prudhvibelide/BLE-Fitness-Tracker/Firmware/config/pin_config.h

#ifndef PIN_CONFIG_H
#define PIN_CONFIG_H

// $[CMU]
// [CMU]$

// $[LFXO]
// LFXO LFXTAL_I on PD01
#ifndef LFXO_LFXTAL_I_PORT                      
#define LFXO_LFXTAL_I_PORT                       gpioPortD
#endif
#ifndef LFXO_LFXTAL_I_PIN                       
#define LFXO_LFXTAL_I_PIN                        1
#endif

// LFXO LFXTAL_O on PD00
#ifndef LFXO_LFXTAL_O_PORT                      
#define LFXO_LFXTAL_O_PORT                       gpioPortD
#endif
#ifndef LFXO_LFXTAL_O_PIN                       
#define LFXO_LFXTAL_O_PIN                        0
#endif

// [LFXO]$

// $[PRS.ASYNCH0]
// [PRS.ASYNCH0]$

// $[PRS.ASYNCH1]
// [PRS.ASYNCH1]$

// $[PRS.ASYNCH2]
// [PRS.ASYNCH2]$

// $[PRS.ASYNCH3]
// [PRS.ASYNCH3]$

// $[PRS.ASYNCH4]
// [PRS.ASYNCH4]$

// $[PRS.ASYNCH5]
// [PRS.ASYNCH5]$

// $[PRS.ASYNCH6]
// [PRS.ASYNCH6]$

// $[PRS.ASYNCH7]
// [PRS.ASYNCH7]$

// $[PRS.ASYNCH8]
// [PRS.ASYNCH8]$

// $[PRS.ASYNCH9]
// [PRS.ASYNCH9]$

// $[PRS.ASYNCH10]
// [PRS.ASYNCH10]$

// $[PRS.ASYNCH11]
// [PRS.ASYNCH11]$

// $[PRS.ASYNCH12]
// [PRS.ASYNCH12]$

// $[PRS.ASYNCH13]
// [PRS.ASYNCH13]$

// $[PRS.ASYNCH14]
// [PRS.ASYNCH14]$

// $[PRS.ASYNCH15]
// [PRS.ASYNCH15]$

// $[PRS.SYNCH0]
// [PRS.SYNCH0]$

// $[PRS.SYNCH1]
// [PRS.SYNCH1]$

// $[PRS.SYNCH2]
// [PRS.SYNCH2]$

// $[PRS.SYNCH3]
// [PRS.SYNCH3]$

// $[GPIO]
// [GPIO]$

// $[TIMER0]
// [TIMER0]$

// $[TIMER1]
// [TIMER1]$

// $[TIMER2]
// [TIMER2]$

// $[TIMER3]
// [TIMER3]$

// $[TIMER4]
// [TIMER4]$

// $[USART0]
// [USART0]$

// $[I2C1]
// [I2C1]$

// $[EUSART1]
// [EUSART1]$

// $[KEYSCAN]
// [KEYSCAN]$

// $[LETIMER0]
// [LETIMER0]$

// $[IADC0]
// [IADC0]$

// $[ACMP0]
// [ACMP0]$

// $[ACMP1]
// [ACMP1]$

// $[VDAC0]
// [VDAC0]$

// $[VDAC1]
// [VDAC1]$

// $[PCNT0]
// [PCNT0]$

// $[HFXO0]
// [HFXO0]$

// $[I2C0]
// [I2C0]$

// $[EUSART0]
// [EUSART0]$

// $[PTI]
// [PTI]$

// $[MODEM]
// [MODEM]$

// $[CUSTOM_PIN_NAME]
#ifndef _PORT                                   
#define _PORT                                    gpioPortA
#endif
#ifndef _PIN                                    
#define _PIN                                     0
#endif

// [CUSTOM_PIN_NAME]$

#endif // PIN_CONFIG_H
