prudhvibelide/BLE-Fitness-Tracker/Firmware/gecko_sdk_4.4.4/platform/emlib/inc/em_adc.h

/***************************************************************************//**
 * @file
 * @brief Analog to Digital Converter (ADC) peripheral API
 *******************************************************************************
 * # License
 * <b>Copyright 2018 Silicon Laboratories Inc. www.silabs.com</b>
 *******************************************************************************
 *
 * SPDX-License-Identifier: Zlib
 *
 * The licensor of this software is Silicon Laboratories Inc.
 *
 * This software is provided 'as-is', without any express or implied
 * warranty. In no event will the authors be held liable for any damages
 * arising from the use of this software.
 *
 * Permission is granted to anyone to use this software for any purpose,
 * including commercial applications, and to alter it and redistribute it
 * freely, subject to the following restrictions:
 *
 * 1. The origin of this software must not be misrepresented; you must not
 *    claim that you wrote the original software. If you use this software
 *    in a product, an acknowledgment in the product documentation would be
 *    appreciated but is not required.
 * 2. Altered source versions must be plainly marked as such, and must not be
 *    misrepresented as being the original software.
 * 3. This notice may not be removed or altered from any source distribution.
 *
 ******************************************************************************/

#ifndef EM_ADC_H
#define EM_ADC_H

#include "em_device.h"
#if defined(ADC_COUNT) && (ADC_COUNT > 0)

#include <stdbool.h>

#ifdef __cplusplus
extern "C" {
#endif

/***************************************************************************//**
 * @addtogroup adc
 * @{
 ******************************************************************************/

/*******************************************************************************
 ********************************   ENUMS   ************************************
 ******************************************************************************/

/** Acquisition time (in ADC clock cycles). */
typedef enum {
  adcAcqTime1   = _ADC_SINGLECTRL_AT_1CYCLE,    /**< 1 clock cycle. */
  adcAcqTime2   = _ADC_SINGLECTRL_AT_2CYCLES,   /**< 2 clock cycles. */
  adcAcqTime4   = _ADC_SINGLECTRL_AT_4CYCLES,   /**< 4 clock cycles. */
  adcAcqTime8   = _ADC_SINGLECTRL_AT_8CYCLES,   /**< 8 clock cycles. */
  adcAcqTime16  = _ADC_SINGLECTRL_AT_16CYCLES,  /**< 16 clock cycles. */
  adcAcqTime32  = _ADC_SINGLECTRL_AT_32CYCLES,  /**< 32 clock cycles. */
  adcAcqTime64  = _ADC_SINGLECTRL_AT_64CYCLES,  /**< 64 clock cycles. */
  adcAcqTime128 = _ADC_SINGLECTRL_AT_128CYCLES, /**< 128 clock cycles. */
  adcAcqTime256 = _ADC_SINGLECTRL_AT_256CYCLES  /**< 256 clock cycles. */
} ADC_AcqTime_TypeDef;

#if defined(_ADC_CTRL_LPFMODE_MASK)
/** Lowpass filter mode. */
typedef enum {
  /** No filter or decoupling capacitor. */
  adcLPFilterBypass = _ADC_CTRL_LPFMODE_BYPASS,

  /** On-chip RC filter. */
  adcLPFilterRC     = _ADC_CTRL_LPFMODE_RCFILT,

  /** On-chip decoupling capacitor. */
  adcLPFilterDeCap  = _ADC_CTRL_LPFMODE_DECAP
} ADC_LPFilter_TypeDef;
#endif

/** Oversample rate select. */
typedef enum {
  /** 2 samples per conversion result. */
  adcOvsRateSel2    = _ADC_CTRL_OVSRSEL_X2,

  /** 4 samples per conversion result. */
  adcOvsRateSel4    = _ADC_CTRL_OVSRSEL_X4,

  /** 8 samples per conversion result. */
  adcOvsRateSel8    = _ADC_CTRL_OVSRSEL_X8,

  /** 16 samples per conversion result. */
  adcOvsRateSel16   = _ADC_CTRL_OVSRSEL_X16,

  /** 32 samples per conversion result. */
  adcOvsRateSel32   = _ADC_CTRL_OVSRSEL_X32,

  /** 64 samples per conversion result. */
  adcOvsRateSel64   = _ADC_CTRL_OVSRSEL_X64,

  /** 128 samples per conversion result. */
  adcOvsRateSel128  = _ADC_CTRL_OVSRSEL_X128,

  /** 256 samples per conversion result. */
  adcOvsRateSel256  = _ADC_CTRL_OVSRSEL_X256,

  /** 512 samples per conversion result. */
  adcOvsRateSel512  = _ADC_CTRL_OVSRSEL_X512,

  /** 1024 samples per conversion result. */
  adcOvsRateSel1024 = _ADC_CTRL_OVSRSEL_X1024,

  /** 2048 samples per conversion result. */
  adcOvsRateSel2048 = _ADC_CTRL_OVSRSEL_X2048,

  /** 4096 samples per conversion result. */
  adcOvsRateSel4096 = _ADC_CTRL_OVSRSEL_X4096
} ADC_OvsRateSel_TypeDef;

/** Peripheral Reflex System signal used to trigger a single sample. */
typedef enum {
#if defined(_ADC_SINGLECTRL_PRSSEL_MASK)
  adcPRSSELCh0 = _ADC_SINGLECTRL_PRSSEL_PRSCH0, /**< PRS channel 0. */
  adcPRSSELCh1 = _ADC_SINGLECTRL_PRSSEL_PRSCH1, /**< PRS channel 1. */
  adcPRSSELCh2 = _ADC_SINGLECTRL_PRSSEL_PRSCH2, /**< PRS channel 2. */
  adcPRSSELCh3 = _ADC_SINGLECTRL_PRSSEL_PRSCH3, /**< PRS channel 3. */
#if defined(_ADC_SINGLECTRL_PRSSEL_PRSCH4)
  adcPRSSELCh4 = _ADC_SINGLECTRL_PRSSEL_PRSCH4, /**< PRS channel 4. */
#endif
#if defined(_ADC_SINGLECTRL_PRSSEL_PRSCH5)
  adcPRSSELCh5 = _ADC_SINGLECTRL_PRSSEL_PRSCH5, /**< PRS channel 5. */
#endif
#if defined(_ADC_SINGLECTRL_PRSSEL_PRSCH6)
  adcPRSSELCh6 = _ADC_SINGLECTRL_PRSSEL_PRSCH6, /**< PRS channel 6. */
#endif
#if defined(_ADC_SINGLECTRL_PRSSEL_PRSCH7)
  adcPRSSELCh7 = _ADC_SINGLECTRL_PRSSEL_PRSCH7, /**< PRS channel 7. */
#endif
#if defined(_ADC_SINGLECTRL_PRSSEL_PRSCH8)
  adcPRSSELCh8 = _ADC_SINGLECTRL_PRSSEL_PRSCH8, /**< PRS channel 8. */
#endif
#if defined(_ADC_SINGLECTRL_PRSSEL_PRSCH9)
  adcPRSSELCh9 = _ADC_SINGLECTRL_PRSSEL_PRSCH9, /**< PRS channel 9. */
#endif
#if defined(_ADC_SINGLECTRL_PRSSEL_PRSCH10)
  adcPRSSELCh10 = _ADC_SINGLECTRL_PRSSEL_PRSCH10, /**< PRS channel 10. */
#endif
#if defined(_ADC_SINGLECTRL_PRSSEL_PRSCH11)
  adcPRSSELCh11 = _ADC_SINGLECTRL_PRSSEL_PRSCH11, /**< PRS channel 11. */
#endif
#elif defined(_ADC_SINGLECTRLX_PRSSEL_MASK)
  adcPRSSELCh0 = _ADC_SINGLECTRLX_PRSSEL_PRSCH0, /**< PRS channel 0. */
  adcPRSSELCh1 = _ADC_SINGLECTRLX_PRSSEL_PRSCH1, /**< PRS channel 1. */
  adcPRSSELCh2 = _ADC_SINGLECTRLX_PRSSEL_PRSCH2, /**< PRS channel 2. */
  adcPRSSELCh3 = _ADC_SINGLECTRLX_PRSSEL_PRSCH3, /**< PRS channel 3. */
  adcPRSSELCh4 = _ADC_SINGLECTRLX_PRSSEL_PRSCH4, /**< PRS channel 4. */
  adcPRSSELCh5 = _ADC_SINGLECTRLX_PRSSEL_PRSCH5, /**< PRS channel 5. */
  adcPRSSELCh6 = _ADC_SINGLECTRLX_PRSSEL_PRSCH6, /**< PRS channel 6. */
  adcPRSSELCh7 = _ADC_SINGLECTRLX_PRSSEL_PRSCH7,  /**< PRS channel 7. */
#if defined(_ADC_SINGLECTRLX_PRSSEL_PRSCH8)
  adcPRSSELCh8 = _ADC_SINGLECTRLX_PRSSEL_PRSCH8,  /**< PRS channel 8. */
#endif
#if defined(_ADC_SINGLECTRLX_PRSSEL_PRSCH9)
  adcPRSSELCh9 = _ADC_SINGLECTRLX_PRSSEL_PRSCH9,  /**< PRS channel 9. */
#endif
#if defined(_ADC_SINGLECTRLX_PRSSEL_PRSCH10)
  adcPRSSELCh10 = _ADC_SINGLECTRLX_PRSSEL_PRSCH10,  /**< PRS channel 10. */
#endif
#if defined(_ADC_SINGLECTRLX_PRSSEL_PRSCH11)
  adcPRSSELCh11 = _ADC_SINGLECTRLX_PRSSEL_PRSCH11,  /**< PRS channel 11. */
#endif
#if defined(_ADC_SINGLECTRLX_PRSSEL_PRSCH12)
  adcPRSSELCh12 = _ADC_SINGLECTRLX_PRSSEL_PRSCH12,  /**< PRS channel 12. */
  adcPRSSELCh13 = _ADC_SINGLECTRLX_PRSSEL_PRSCH13,  /**< PRS channel 13. */
  adcPRSSELCh14 = _ADC_SINGLECTRLX_PRSSEL_PRSCH14,  /**< PRS channel 14. */
  adcPRSSELCh15 = _ADC_SINGLECTRLX_PRSSEL_PRSCH15,  /**< PRS channel 15. */
#endif
#endif
} ADC_PRSSEL_TypeDef;

/** Single and scan mode voltage references. Using unshifted enumerations and or
    in ADC_CTRLX_VREFSEL_REG to select the extension register CTRLX_VREFSEL. */
#if defined(_ADC_SCANCTRLX_VREFSEL_MASK)
#define ADC_CTRLX_VREFSEL_REG     0x80UL
#endif
/** ADC Reference */
typedef enum {
  /** Internal 1.25 V reference. */
  adcRef1V25      = _ADC_SINGLECTRL_REF_1V25,

  /** Internal 2.5 V reference. */
  adcRef2V5       = _ADC_SINGLECTRL_REF_2V5,

  /** Buffered VDD. */
  adcRefVDD       = _ADC_SINGLECTRL_REF_VDD,

#if defined(_ADC_SINGLECTRL_REF_5VDIFF)
  /** Internal differential 5 V reference. */
  adcRef5VDIFF    = _ADC_SINGLECTRL_REF_5VDIFF,
#endif

#if defined(_ADC_SINGLECTRL_REF_5V)
  /** Internal 5 V reference. */
  adcRef5V        = _ADC_SINGLECTRL_REF_5V,
#endif

  /** Single-ended external reference from pin 6. */
  adcRefExtSingle = _ADC_SINGLECTRL_REF_EXTSINGLE,

  /** Differential external reference from pin 6 and 7. */
  adcRef2xExtDiff = _ADC_SINGLECTRL_REF_2XEXTDIFF,

  /** Unbuffered 2xVDD. */
  adcRef2xVDD     = _ADC_SINGLECTRL_REF_2XVDD,

#if defined(_ADC_SINGLECTRLX_VREFSEL_VBGR)
  /** Custom VFS: Internal Bandgap reference. */
  adcRefVBGR      = _ADC_SINGLECTRLX_VREFSEL_VBGR | ADC_CTRLX_VREFSEL_REG,
#endif

#if defined(_ADC_SINGLECTRLX_VREFSEL_VDDXWATT)
  /** Custom VFS: Scaled AVDD: AVDD * VREFATT. */
  adcRefVddxAtt   = _ADC_SINGLECTRLX_VREFSEL_VDDXWATT | ADC_CTRLX_VREFSEL_REG,
#endif

#if defined(_ADC_SINGLECTRLX_VREFSEL_VREFPWATT)
  /** Custom VFS: Scaled singled ended external reference from pin 6:
      VREFP * VREFATT. */
  adcRefVPxAtt    = _ADC_SINGLECTRLX_VREFSEL_VREFPWATT | ADC_CTRLX_VREFSEL_REG,
#endif

#if defined(_ADC_SINGLECTRLX_VREFSEL_VREFP)
  /** Custom VFS: Raw single-ended external reference from pin 6. */
  adcRefP         = _ADC_SINGLECTRLX_VREFSEL_VREFP | ADC_CTRLX_VREFSEL_REG,
#endif

#if defined(_ADC_SINGLECTRLX_VREFSEL_VENTROPY)
  /** Custom VFS: Special mode for entropy generation */
  adcRefVEntropy = _ADC_SINGLECTRLX_VREFSEL_VENTROPY | ADC_CTRLX_VREFSEL_REG,
#endif

#if defined(_ADC_SINGLECTRLX_VREFSEL_VREFPNWATT)
  /** Custom VFS: Scaled differential external Vref from pin 6 and 7:
      (VREFP - VREFN) * VREFATT. */
  adcRefVPNxAtt  = _ADC_SINGLECTRLX_VREFSEL_VREFPNWATT | ADC_CTRLX_VREFSEL_REG,
#endif

#if defined(_ADC_SINGLECTRLX_VREFSEL_VREFPN)
  /** Custom VFS: Raw differential external Vref from pin 6 and 7:
      VREFP - VREFN. */
  adcRefPN       = _ADC_SINGLECTRLX_VREFSEL_VREFPN | ADC_CTRLX_VREFSEL_REG,
#endif
} ADC_Ref_TypeDef;

/** @cond DO_NOT_INCLUDE_WITH_DOXYGEN */
/* Deprecated enum names */
#if !defined(_ADC_SINGLECTRL_REF_5VDIFF)
#define adcRef5VDIFF adcRef5V
#endif
/** @endcond */

/** Sample resolution. */
typedef enum {
  adcRes12Bit = _ADC_SINGLECTRL_RES_12BIT, /**< 12 bit sampling. */
  adcRes8Bit  = _ADC_SINGLECTRL_RES_8BIT,  /**< 8 bit sampling. */
  adcRes6Bit  = _ADC_SINGLECTRL_RES_6BIT,  /**< 6 bit sampling. */
  adcResOVS   = _ADC_SINGLECTRL_RES_OVS    /**< Oversampling. */
} ADC_Res_TypeDef;

#if defined(_ADC_SINGLECTRL_INPUTSEL_MASK)
/** Single sample input selection. */
typedef enum {
  /* Differential mode disabled */
  adcSingleInputCh0      = _ADC_SINGLECTRL_INPUTSEL_CH0,      /**< Channel 0. */
  adcSingleInputCh1      = _ADC_SINGLECTRL_INPUTSEL_CH1,      /**< Channel 1. */
  adcSingleInputCh2      = _ADC_SINGLECTRL_INPUTSEL_CH2,      /**< Channel 2. */
  adcSingleInputCh3      = _ADC_SINGLECTRL_INPUTSEL_CH3,      /**< Channel 3. */
  adcSingleInputCh4      = _ADC_SINGLECTRL_INPUTSEL_CH4,      /**< Channel 4. */
  adcSingleInputCh5      = _ADC_SINGLECTRL_INPUTSEL_CH5,      /**< Channel 5. */
  adcSingleInputCh6      = _ADC_SINGLECTRL_INPUTSEL_CH6,      /**< Channel 6. */
  adcSingleInputCh7      = _ADC_SINGLECTRL_INPUTSEL_CH7,      /**< Channel 7. */
  adcSingleInputTemp     = _ADC_SINGLECTRL_INPUTSEL_TEMP,     /**< Temperature reference. */
  adcSingleInputVDDDiv3  = _ADC_SINGLECTRL_INPUTSEL_VDDDIV3,  /**< VDD divided by 3. */
  adcSingleInputVDD      = _ADC_SINGLECTRL_INPUTSEL_VDD,      /**< VDD. */
  adcSingleInputVSS      = _ADC_SINGLECTRL_INPUTSEL_VSS,      /**< VSS. */
  adcSingleInputVrefDiv2 = _ADC_SINGLECTRL_INPUTSEL_VREFDIV2, /**< Vref divided by 2. */
  adcSingleInputDACOut0  = _ADC_SINGLECTRL_INPUTSEL_DAC0OUT0, /**< DAC output 0. */
  adcSingleInputDACOut1  = _ADC_SINGLECTRL_INPUTSEL_DAC0OUT1, /**< DAC output 1. */
  adcSingleInputATEST    = 15,                                /**< ATEST. */

  /* Differential mode enabled */
  adcSingleInputCh0Ch1   = _ADC_SINGLECTRL_INPUTSEL_CH0CH1,   /**< Positive Ch0, negative Ch1. */
  adcSingleInputCh2Ch3   = _ADC_SINGLECTRL_INPUTSEL_CH2CH3,   /**< Positive Ch2, negative Ch3. */
  adcSingleInputCh4Ch5   = _ADC_SINGLECTRL_INPUTSEL_CH4CH5,   /**< Positive Ch4, negative Ch5. */
  adcSingleInputCh6Ch7   = _ADC_SINGLECTRL_INPUTSEL_CH6CH7,   /**< Positive Ch6, negative Ch7. */
  adcSingleInputDiff0    = 4                                  /**< Differential 0. */
} ADC_SingleInput_TypeDef;

/** @cond DO_NOT_INCLUDE_WITH_DOXYGEN */
/* Deprecated enum names */
#define adcSingleInpCh0       adcSingleInputCh0
#define adcSingleInpCh1       adcSingleInputCh1
#define adcSingleInpCh2       adcSingleInputCh2
#define adcSingleInpCh3       adcSingleInputCh3
#define adcSingleInpCh4       adcSingleInputCh4
#define adcSingleInpCh5       adcSingleInputCh5
#define adcSingleInpCh6       adcSingleInputCh6
#define adcSingleInpCh7       adcSingleInputCh7
#define adcSingleInpTemp      adcSingleInputTemp
#define adcSingleInpVDDDiv3   adcSingleInputVDDDiv3
#define adcSingleInpVDD       adcSingleInputVDD
#define adcSingleInpVSS       adcSingleInputVSS
#define adcSingleInpVrefDiv2  adcSingleInputVrefDiv2
#define adcSingleInpDACOut0   adcSingleInputDACOut0
#define adcSingleInpDACOut1   adcSingleInputDACOut1
#define adcSingleInpATEST     adcSingleInputATEST
#define adcSingleInpCh0Ch1    adcSingleInputCh0Ch1
#define adcSingleInpCh2Ch3    adcSingleInputCh2Ch3
#define adcSingleInpCh4Ch5    adcSingleInputCh4Ch5
#define adcSingleInpCh6Ch7    adcSingleInputCh6Ch7
#define adcSingleInpDiff0     adcSingleInputDiff0
/** @endcond */
#endif

#if defined(_ADC_SINGLECTRL_POSSEL_MASK)
/** Positive input selection for single and scan conversion. */
typedef enum {
  adcPosSelAPORT0XCH0  = _ADC_SINGLECTRL_POSSEL_APORT0XCH0,
  adcPosSelAPORT0XCH1  = _ADC_SINGLECTRL_POSSEL_APORT0XCH1,
  adcPosSelAPORT0XCH2  = _ADC_SINGLECTRL_POSSEL_APORT0XCH2,
  adcPosSelAPORT0XCH3  = _ADC_SINGLECTRL_POSSEL_APORT0XCH3,
  adcPosSelAPORT0XCH4  = _ADC_SINGLECTRL_POSSEL_APORT0XCH4,
  adcPosSelAPORT0XCH5  = _ADC_SINGLECTRL_POSSEL_APORT0XCH5,
  adcPosSelAPORT0XCH6  = _ADC_SINGLECTRL_POSSEL_APORT0XCH6,
  adcPosSelAPORT0XCH7  = _ADC_SINGLECTRL_POSSEL_APORT0XCH7,
  adcPosSelAPORT0XCH8  = _ADC_SINGLECTRL_POSSEL_APORT0XCH8,
  adcPosSelAPORT0XCH9  = _ADC_SINGLECTRL_POSSEL_APORT0XCH9,
  adcPosSelAPORT0XCH10 = _ADC_SINGLECTRL_POSSEL_APORT0XCH10,
  adcPosSelAPORT0XCH11 = _ADC_SINGLECTRL_POSSEL_APORT0XCH11,
  adcPosSelAPORT0XCH12 = _ADC_SINGLECTRL_POSSEL_APORT0XCH12,
  adcPosSelAPORT0XCH13 = _ADC_SINGLECTRL_POSSEL_APORT0XCH13,
  adcPosSelAPORT0XCH14 = _ADC_SINGLECTRL_POSSEL_APORT0XCH14,
  adcPosSelAPORT0XCH15 = _ADC_SINGLECTRL_POSSEL_APORT0XCH15,
  adcPosSelAPORT0YCH0  = _ADC_SINGLECTRL_POSSEL_APORT0YCH0,
  adcPosSelAPORT0YCH1  = _ADC_SINGLECTRL_POSSEL_APORT0YCH1,
  adcPosSelAPORT0YCH2  = _ADC_SINGLECTRL_POSSEL_APORT0YCH2,
  adcPosSelAPORT0YCH3  = _ADC_SINGLECTRL_POSSEL_APORT0YCH3,
  adcPosSelAPORT0YCH4  = _ADC_SINGLECTRL_POSSEL_APORT0YCH4,
  adcPosSelAPORT0YCH5  = _ADC_SINGLECTRL_POSSEL_APORT0YCH5,
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
  adcPosSelAPORT4XCH13 = _ADC_SINGLECTRL_POSSEL_APORT4XCH13,
  adcPosSelAPORT4YCH14 = _ADC_SINGLECTRL_POSSEL_APORT4YCH14,
  adcPosSelAPORT4XCH15 = _ADC_SINGLECTRL_POSSEL_APORT4XCH15,
  adcPosSelAPORT4YCH16 = _ADC_SINGLECTRL_POSSEL_APORT4YCH16,
  adcPosSelAPORT4XCH17 = _ADC_SINGLECTRL_POSSEL_APORT4XCH17,
  adcPosSelAPORT4YCH18 = _ADC_SINGLECTRL_POSSEL_APORT4YCH18,
  adcPosSelAPORT4XCH19 = _ADC_SINGLECTRL_POSSEL_APORT4XCH19,
  adcPosSelAPORT4YCH20 = _ADC_SINGLECTRL_POSSEL_APORT4YCH20,
  adcPosSelAPORT4XCH21 = _ADC_SINGLECTRL_POSSEL_APORT4XCH21,
  adcPosSelAPORT4YCH22 = _ADC_SINGLECTRL_POSSEL_APORT4YCH22,
  adcPosSelAPORT4XCH23 = _ADC_SINGLECTRL_POSSEL_APORT4XCH23,
  adcPosSelAPORT4YCH24 = _ADC_SINGLECTRL_POSSEL_APORT4YCH24,
  adcPosSelAPORT4XCH25 = _ADC_SINGLECTRL_POSSEL_APORT4XCH25,
  adcPosSelAPORT4YCH26 = _ADC_SINGLECTRL_POSSEL_APORT4YCH26,
  adcPosSelAPORT4XCH27 = _ADC_SINGLECTRL_POSSEL_APORT4XCH27,
  adcPosSelAPORT4YCH28 = _ADC_SINGLECTRL_POSSEL_APORT4YCH28,
  adcPosSelAPORT4XCH29 = _ADC_SINGLECTRL_POSSEL_APORT4XCH29,
  adcPosSelAPORT4YCH30 = _ADC_SINGLECTRL_POSSEL_APORT4YCH30,
  adcPosSelAPORT4XCH31 = _ADC_SINGLECTRL_POSSEL_APORT4XCH31,
  adcPosSelAVDD        = _ADC_SINGLECTRL_POSSEL_AVDD,
  adcPosSelBUVDD       = _ADC_SINGLECTRL_POSSEL_BUVDD,
  adcPosSelDVDD        = _ADC_SINGLECTRL_POSSEL_DVDD,
  adcPosSelPAVDD       = _ADC_SINGLECTRL_POSSEL_PAVDD,
  adcPosSelDECOUPLE    = _ADC_SINGLECTRL_POSSEL_DECOUPLE,
  adcPosSelIOVDD       = _ADC_SINGLECTRL_POSSEL_IOVDD,
  adcPosSelIOVDD1      = _ADC_SINGLECTRL_POSSEL_IOVDD1,
  adcPosSelVSP         = _ADC_SINGLECTRL_POSSEL_VSP,
  adcPosSelOPA2        = _ADC_SINGLECTRL_POSSEL_OPA2,
  adcPosSelTEMP        = _ADC_SINGLECTRL_POSSEL_TEMP,
  adcPosSelDAC0OUT0    = _ADC_SINGLECTRL_POSSEL_DAC0OUT0,
  adcPosSelR5VOUT      = _ADC_SINGLECTRL_POSSEL_R5VOUT,
  adcPosSelSP1         = _ADC_SINGLECTRL_POSSEL_SP1,
  adcPosSelSP2         = _ADC_SINGLECTRL_POSSEL_SP2,
  adcPosSelDAC0OUT1    = _ADC_SINGLECTRL_POSSEL_DAC0OUT1,
  adcPosSelSUBLSB      = _ADC_SINGLECTRL_POSSEL_SUBLSB,
  adcPosSelOPA3        = _ADC_SINGLECTRL_POSSEL_OPA3,
  adcPosSelDEFAULT     = _ADC_SINGLECTRL_POSSEL_DEFAULT,
  adcPosSelVSS         = _ADC_SINGLECTRL_POSSEL_VSS
} ADC_PosSel_TypeDef;

/* Map legacy or incorrectly named select enums to correct enums. */
/** @cond DO_NOT_INCLUDE_WITH_DOXYGEN */
#define adcPosSelIO0            adcPosSelIOVDD
#define adcPosSelVREGOUTPA      adcPosSelPAVDD
#define adcPosSelAREG           adcPosSelDVDD
#define adcPosSelPDBU           adcPosSelDECOUPLE
/** @endcond */
#endif

#if defined(_ADC_SINGLECTRL_NEGSEL_MASK)
/** Negative input selection for single and scan conversion. */
typedef enum {
  adcNegSelAPORT0XCH0  = _ADC_SINGLECTRL_NEGSEL_APORT0XCH0,
  adcNegSelAPORT0XCH1  = _ADC_SINGLECTRL_NEGSEL_APORT0XCH1,
  adcNegSelAPORT0XCH2  = _ADC_SINGLECTRL_NEGSEL_APORT0XCH2,
  adcNegSelAPORT0XCH3  = _ADC_SINGLECTRL_NEGSEL_APORT0XCH3,
  adcNegSelAPORT0XCH4  = _ADC_SINGLECTRL_NEGSEL_APORT0XCH4,
  adcNegSelAPORT0XCH5  = _ADC_SINGLECTRL_NEGSEL_APORT0XCH5,
  adcNegSelAPORT0XCH6  = _ADC_SINGLECTRL_NEGSEL_APORT0XCH6,
  adcNegSelAPORT0XCH7  = _ADC_SINGLECTRL_NEGSEL_APORT0XCH7,
  adcNegSelAPORT0XCH8  = _ADC_SINGLECTRL_NEGSEL_APORT0XCH8,
  adcNegSelAPORT0XCH9  = _ADC_SINGLECTRL_NEGSEL_APORT0XCH9,
  adcNegSelAPORT0XCH10 = _ADC_SINGLECTRL_NEGSEL_APORT0XCH10,
  adcNegSelAPORT0XCH11 = _ADC_SINGLECTRL_NEGSEL_APORT0XCH11,
  adcNegSelAPORT0XCH12 = _ADC_SINGLECTRL_NEGSEL_APORT0XCH12,
  adcNegSelAPORT0XCH13 = _ADC_SINGLECTRL_NEGSEL_APORT0XCH13,
  adcNegSelAPORT0XCH14 = _ADC_SINGLECTRL_NEGSEL_APORT0XCH14,
  adcNegSelAPORT0XCH15 = _ADC_SINGLECTRL_NEGSEL_APORT0XCH15,
  adcNegSelAPORT0YCH0  = _ADC_SINGLECTRL_NEGSEL_APORT0YCH0,
  adcNegSelAPORT0YCH1  = _ADC_SINGLECTRL_NEGSEL_APORT0YCH1,
  adcNegSelAPORT0YCH2  = _ADC_SINGLECTRL_NEGSEL_APORT0YCH2,
  adcNegSelAPORT0YCH3  = _ADC_SINGLECTRL_NEGSEL_APORT0YCH3,
  adcNegSelAPORT0YCH4  = _ADC_SINGLECTRL_NEGSEL_APORT0YCH4,
  adcNegSelAPORT0YCH5  = _ADC_SINGLECTRL_NEGSEL_APORT0YCH5,
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
  adcNegSelAPORT4XCH13 = _ADC_SINGLECTRL_NEGSEL_APORT4XCH13,
  adcNegSelAPORT4YCH14 = _ADC_SINGLECTRL_NEGSEL_APORT4YCH14,
  adcNegSelAPORT4XCH15 = _ADC_SINGLECTRL_NEGSEL_APORT4XCH15,
  adcNegSelAPORT4YCH16 = _ADC_SINGLECTRL_NEGSEL_APORT4YCH16,
  adcNegSelAPORT4XCH17 = _ADC_SINGLECTRL_NEGSEL_APORT4XCH17,
  adcNegSelAPORT4YCH18 = _ADC_SINGLECTRL_NEGSEL_APORT4YCH18,
  adcNegSelAPORT4XCH19 = _ADC_SINGLECTRL_NEGSEL_APORT4XCH19,
  adcNegSelAPORT4YCH20 = _ADC_SINGLECTRL_NEGSEL_APORT4YCH20,
  adcNegSelAPORT4XCH21 = _ADC_SINGLECTRL_NEGSEL_APORT4XCH21,
  adcNegSelAPORT4YCH22 = _ADC_SINGLECTRL_NEGSEL_APORT4YCH22,
  adcNegSelAPORT4XCH23 = _ADC_SINGLECTRL_NEGSEL_APORT4XCH23,
  adcNegSelAPORT4YCH24 = _ADC_SINGLECTRL_NEGSEL_APORT4YCH24,
  adcNegSelAPORT4XCH25 = _ADC_SINGLECTRL_NEGSEL_APORT4XCH25,
  adcNegSelAPORT4YCH26 = _ADC_SINGLECTRL_NEGSEL_APORT4YCH26,
  adcNegSelAPORT4XCH27 = _ADC_SINGLECTRL_NEGSEL_APORT4XCH27,
  adcNegSelAPORT4YCH28 = _ADC_SINGLECTRL_NEGSEL_APORT4YCH28,
  adcNegSelAPORT4XCH29 = _ADC_SINGLECTRL_NEGSEL_APORT4XCH29,
  adcNegSelAPORT4YCH30 = _ADC_SINGLECTRL_NEGSEL_APORT4YCH30,
  adcNegSelAPORT4XCH31 = _ADC_SINGLECTRL_NEGSEL_APORT4XCH31,
  adcNegSelTESTN       = _ADC_SINGLECTRL_NEGSEL_TESTN,
  adcNegSelDEFAULT     = _ADC_SINGLECTRL_NEGSEL_DEFAULT,
  adcNegSelVSS         = _ADC_SINGLECTRL_NEGSEL_VSS
} ADC_NegSel_TypeDef;
#endif

#if defined(_ADC_SCANINPUTSEL_MASK)
/** ADC scan input groups. */
typedef enum {
  adcScanInputGroup0 = 0,
  adcScanInputGroup1 = 1,
  adcScanInputGroup2 = 2,
  adcScanInputGroup3 = 3,
} ADC_ScanInputGroup_TypeDef;

/** Define none selected group for ADC_SCANINPUTSEL. */
#define ADC_SCANINPUTSEL_GROUP_NONE     0xFFU
/** Define none selected for ADC_SCANINPUTSEL. */
#define ADC_SCANINPUTSEL_NONE           ((ADC_SCANINPUTSEL_GROUP_NONE                  \
                                          << _ADC_SCANINPUTSEL_INPUT0TO7SEL_SHIFT)     \
                                         | (ADC_SCANINPUTSEL_GROUP_NONE                \
                                            << _ADC_SCANINPUTSEL_INPUT8TO15SEL_SHIFT)  \
                                         | (ADC_SCANINPUTSEL_GROUP_NONE                \
                                            << _ADC_SCANINPUTSEL_INPUT16TO23SEL_SHIFT) \
                                         | (ADC_SCANINPUTSEL_GROUP_NONE                \
                                            << _ADC_SCANINPUTSEL_INPUT24TO31SEL_SHIFT))

/** ADC scan alternative negative inputs. */
typedef enum {
  adcScanNegInput1  = 1,
  adcScanNegInput3  = 3,
  adcScanNegInput5  = 5,
  adcScanNegInput7  = 7,
  adcScanNegInput8  = 8,
  adcScanNegInput10 = 10,
  adcScanNegInput12 = 12,
  adcScanNegInput14 = 14,
  adcScanNegInputDefault = 0xFF,
} ADC_ScanNegInput_TypeDef;
#endif

/** ADC start command. */
typedef enum {
  /** Start a single conversion. */
  adcStartSingle        = ADC_CMD_SINGLESTART,

  /** Start a scan sequence. */
  adcStartScan          = ADC_CMD_SCANSTART,

  /**
   * Start a scan sequence and single conversion, typically used when tailgating
   * a single conversion after a scan sequence.
   */
  adcStartScanAndSingle = ADC_CMD_SCANSTART | ADC_CMD_SINGLESTART
} ADC_Start_TypeDef;

/** Warm-up mode. */
typedef enum {
  /** ADC shutdown after each conversion. */
  adcWarmupNormal          = _ADC_CTRL_WARMUPMODE_NORMAL,

#if defined(_ADC_CTRL_WARMUPMODE_FASTBG)
  /** Do not warm up bandgap references. */
  adcWarmupFastBG          = _ADC_CTRL_WARMUPMODE_FASTBG,
#endif

#if defined(_ADC_CTRL_WARMUPMODE_KEEPSCANREFWARM)
  /** Reference selected for scan mode kept warm.*/
  adcWarmupKeepScanRefWarm = _ADC_CTRL_WARMUPMODE_KEEPSCANREFWARM,
#endif

#if defined(_ADC_CTRL_WARMUPMODE_KEEPINSTANDBY)
  /** ADC is kept in standby mode between conversions. 1 us warmup time needed
      before the next conversion. */
  adcWarmupKeepInStandby   = _ADC_CTRL_WARMUPMODE_KEEPINSTANDBY,
#endif

#if defined(_ADC_CTRL_WARMUPMODE_KEEPINSLOWACC)
  /** ADC is kept in slow acquisition mode between conversions. 1 us warmup
      time needed before the next conversion. */
  adcWarmupKeepInSlowAcq   = _ADC_CTRL_WARMUPMODE_KEEPINSLOWACC,
#endif

  /** ADC and reference selected for scan mode kept at warmup allowing
      continuous conversion. */
  adcWarmupKeepADCWarm     = _ADC_CTRL_WARMUPMODE_KEEPADCWARM,
} ADC_Warmup_TypeDef;

#if defined(_ADC_CTRL_ADCCLKMODE_MASK)
/** ADC EM2 clock configuration. */
typedef enum {
  adcEm2Disabled           = 0,
  adcEm2ClockOnDemand      = ADC_CTRL_ADCCLKMODE_ASYNC | ADC_CTRL_ASYNCCLKEN_ASNEEDED,
  adcEm2ClockAlwaysOn      = ADC_CTRL_ADCCLKMODE_ASYNC | ADC_CTRL_ASYNCCLKEN_ALWAYSON,
} ADC_EM2ClockConfig_TypeDef;
#endif

/*******************************************************************************
 *******************************   STRUCTS   ***********************************
 ******************************************************************************/

/** ADC initialization structure, common for single conversion and scan sequence. */
typedef struct {
  /**
   * Oversampling rate select. To have any effect, oversampling must
   * be enabled for single/scan mode.
   */
  ADC_OvsRateSel_TypeDef        ovsRateSel;

#if defined(_ADC_CTRL_LPFMODE_MASK)
  /** Lowpass or decoupling capacitor filter. */
  ADC_LPFilter_TypeDef          lpfMode;
#endif

  /** ADC Warm-up mode. */
  ADC_Warmup_TypeDef            warmUpMode;

  /**
   * Timebase for ADC warm up. Select N to give (N+1) HFPERCLK / HFPERCCLK cycles.
   * (Additional delay is added for bandgap references. See the
   * reference manual for more information.) Normally, N should be selected so that the timebase
   * is at least 1 us. See ADC_TimebaseCalc() to obtain
   * a suggested timebase of, at least, 1 us.
   */
  uint8_t                       timebase;

  /** Clock division factor N, ADC clock = (HFPERCLK or HFPERCCLK) / (N + 1). */
  uint8_t                       prescale;

  /** Enable/disable conversion tailgating. */
  bool                          tailgate;

  /** ADC EM2 clock configuration */
#if defined(_ADC_CTRL_ADCCLKMODE_MASK)
  ADC_EM2ClockConfig_TypeDef    em2ClockConfig;
#endif
} ADC_Init_TypeDef;

/** Default configuration for ADC initialization structure. */
#if defined(_ADC_CTRL_LPFMODE_MASK) && (!defined(_ADC_CTRL_ADCCLKMODE_MASK))
#define ADC_INIT_DEFAULT                                                   \
  {                                                                        \
    adcOvsRateSel2,              /* 2x oversampling (if enabled). */       \
    adcLPFilterBypass,           /* No input filter selected. */           \
    adcWarmupNormal,             /* ADC shutdown after each conversion. */ \
    _ADC_CTRL_TIMEBASE_DEFAULT,  /* Use hardware default value. */         \
    _ADC_CTRL_PRESC_DEFAULT,     /* Use hardware default value. */         \
    false                        /* Do not use tailgate. */                \
  }
#elif (!defined(_ADC_CTRL_LPFMODE_MASK)) && (!defined(_ADC_CTRL_ADCCLKMODE_MASK))
#define ADC_INIT_DEFAULT                                                   \
  {                                                                        \
    adcOvsRateSel2,              /* 2x oversampling (if enabled). */       \
    adcWarmupNormal,             /* ADC shutdown after each conversion. */ \
    _ADC_CTRL_TIMEBASE_DEFAULT,  /* Use hardware default value. */         \
    _ADC_CTRL_PRESC_DEFAULT,     /* Use hardware default value. */         \
    false                        /* Do not use tailgate. */                \
  }
#elif (!defined(_ADC_CTRL_LPFMODE_MASK)) && defined(_ADC_CTRL_ADCCLKMODE_MASK)
#define ADC_INIT_DEFAULT                                                   \
  {                                                                        \
    adcOvsRateSel2,              /* 2x oversampling (if enabled). */       \
    adcWarmupNormal,             /* ADC shutdown after each conversion. */ \
    _ADC_CTRL_TIMEBASE_DEFAULT,  /* Use hardware default value. */         \
    _ADC_CTRL_PRESC_DEFAULT,     /* Use hardware default value. */         \
    false,                       /* Do not use tailgate. */                \
    adcEm2Disabled               /* ADC disabled in EM2. */                \
  }
#endif

/** Scan input configuration. */
typedef struct {
  /** Input range select to be applied to ADC_SCANINPUTSEL. */
  uint32_t            scanInputSel;

  /** Input enable mask. */
  uint32_t            scanInputEn;

  /** Alternative negative input. */
  uint32_t            scanNegSel;
} ADC_InitScanInput_TypeDef;

/** Scan sequence initialization structure. */
typedef struct {
  /**
   * Peripheral reflex system trigger selection. Only applicable if @p prsEnable
   * is enabled.
   */
  ADC_PRSSEL_TypeDef  prsSel;

  /** Acquisition time (in ADC clock cycles). */
  ADC_AcqTime_TypeDef acqTime;

  /**
   * Sample reference selection. Note that, for external references, the
   * ADC calibration register must be set explicitly.
   */
  ADC_Ref_TypeDef     reference;

  /** Sample resolution. */
  ADC_Res_TypeDef     resolution;

#if defined(_ADC_SCANCTRL_INPUTMASK_MASK)
  /**
   * Scan input selection. If single ended (@p diff is false), use logical
   * combination of ADC_SCANCTRL_INPUTMASK_CHx defines. If differential input
   * (@p diff is true), use logical combination of ADC_SCANCTRL_INPUTMASK_CHxCHy
   * defines. (Notice underscore prefix for defines used.)
   */
  uint32_t            input;
#endif

#if defined(_ADC_SCANINPUTSEL_MASK)
  /**
   * Scan input configuration. Use @ref ADC_ScanInputClear(), @ref ADC_ScanSingleEndedInputAdd()
   * or @ref ADC_ScanDifferentialInputAdd() to update this structure.
   */
  ADC_InitScanInput_TypeDef scanInputConfig;
#endif

  /** Select if single-ended or differential input. */
  bool                diff;

  /** Peripheral reflex system trigger enable. */
  bool                prsEnable;

  /** Select if left adjustment should be done. */
  bool                leftAdjust;

  /** Select if continuous conversion until explicit stop. */
  bool                rep;

  /** When true, DMA is available in EM2 for scan conversion */
#if defined(_ADC_CTRL_SCANDMAWU_MASK)
  bool                scanDmaEm2Wu;
#endif

#if defined(_ADC_SCANCTRLX_FIFOOFACT_MASK)
  /** When true, FIFO overwrites old data when full. If false, FIFO discards new data.
      The SINGLEOF IRQ is triggered in both cases. */
  bool                fifoOverwrite;
#endif
} ADC_InitScan_TypeDef;

/** Default configuration for ADC scan initialization structure. */
#if defined(_ADC_SCANCTRL_INPUTMASK_MASK)
#define ADC_INITSCAN_DEFAULT                                                      \
  {                                                                               \
    adcPRSSELCh0,            /* PRS ch0 (if enabled). */                          \
    adcAcqTime1,             /* 1 ADC_CLK cycle acquisition time. */              \
    adcRef1V25,              /* 1.25 V internal reference. */                     \
    adcRes12Bit,             /* 12 bit resolution. */                             \
    0,                       /* No input selected. */                             \
    false,                   /* Single-ended input. */                            \
    false,                   /* PRS disabled. */                                  \
    false,                   /* Right adjust. */                                  \
    false,                   /* Deactivate conversion after one scan sequence. */ \
  }
#endif

#if defined(_ADC_SCANINPUTSEL_MASK)
#define ADC_INITSCAN_DEFAULT                                                          \
  {                                                                                   \
    adcPRSSELCh0,            /* PRS ch0 (if enabled). */                              \
    adcAcqTime1,             /* 1 ADC_CLK cycle acquisition time. */                  \
    adcRef1V25,              /* 1.25 V internal reference. */                         \
    adcRes12Bit,             /* 12 bit resolution. */                                 \
    {                                                                                 \
      /* Initialization should match values set by @ref ADC_ScanInputClear(). */      \
      ADC_SCANINPUTSEL_NONE, /* Default ADC inputs. */                                \
      0,                     /* Default input mask (all off). */                      \
      _ADC_SCANNEGSEL_RESETVALUE,/* Default negative select for positive terminal. */ \
    },                                                                                \
    false,                   /* Single-ended input. */                                \
    false,                   /* PRS disabled. */                                      \
    false,                   /* Right adjust. */                                      \
    false,                   /* Deactivate conversion after one scan sequence. */     \
    false,                   /* No EM2 DMA wakeup from scan FIFO DVL. */              \
    false                    /* Discard new data on full FIFO. */                     \
  }
#endif

/** Single conversion initialization structure. */
typedef struct {
  /**
   * Peripheral reflex system trigger selection. Only applicable if @p prsEnable
   * is enabled.
   */
  ADC_PRSSEL_TypeDef            prsSel;

  /** Acquisition time (in ADC clock cycles). */
  ADC_AcqTime_TypeDef           acqTime;

  /**
   * Sample reference selection. Note that, for external references, the
   * ADC calibration register must be set explicitly.
   */
  ADC_Ref_TypeDef               reference;

  /** Sample resolution. */
  ADC_Res_TypeDef               resolution;

#if defined(_ADC_SINGLECTRL_INPUTSEL_MASK)
  /**
   * Sample input selection, use single-ended or differential input according
   * to setting of @p diff.
   */
  ADC_SingleInput_TypeDef       input;
#endif

#if defined(_ADC_SINGLECTRL_POSSEL_MASK)
  /** Select positive input for single channel conversion mode. */
  ADC_PosSel_TypeDef            posSel;
#endif

#if defined(_ADC_SINGLECTRL_NEGSEL_MASK)
  /** Select negative input for single channel conversion mode. Negative input is grounded
      for single-ended (non-differential) conversion.  */
  ADC_NegSel_TypeDef            negSel;
#endif

  /** Select if single-ended or differential input. */
  bool                          diff;

  /** Peripheral reflex system trigger enable. */
  bool                          prsEnable;

  /** Select if left adjustment should be done. */
  bool                          leftAdjust;

  /** Select if continuous conversion until explicit stop. */
  bool                          rep;

#if defined(_ADC_CTRL_SINGLEDMAWU_MASK)
  /** When true, DMA is available in EM2 for single conversion */
  bool                          singleDmaEm2Wu;
#endif

#if defined(_ADC_SINGLECTRLX_FIFOOFACT_MASK)
  /** When true, FIFO overwrites old data when full. If false, FIFO discards new data.
      The SCANOF IRQ is triggered in both cases. */
  bool                          fifoOverwrite;
#endif
} ADC_InitSingle_TypeDef;

/** Default configuration for ADC single conversion initialization structure. */
#if defined(_ADC_SINGLECTRL_INPUTSEL_MASK)
#define ADC_INITSINGLE_DEFAULT                                                    \
  {                                                                               \
    adcPRSSELCh0,            /* PRS ch0 (if enabled). */                          \
    adcAcqTime1,             /* 1 ADC_CLK cycle acquisition time. */              \
    adcRef1V25,              /* 1.25 V internal reference. */                     \
    adcRes12Bit,             /* 12 bit resolution. */                             \
    adcSingleInpCh0,         /* CH0 input selected. */                            \
    false,                   /* Single-ended input. */                            \
    false,                   /* PRS disabled. */                                  \
    false,                   /* Right adjust. */                                  \
    false                    /* Deactivate conversion after one scan sequence. */ \
  }
#else
#define ADC_INITSINGLE_DEFAULT                                                    \
  {                                                                               \
    adcPRSSELCh0,            /* PRS ch0 (if enabled). */                          \
    adcAcqTime1,             /* 1 ADC_CLK cycle acquisition time. */              \
    adcRef1V25,              /* 1.25 V internal reference. */                     \
    adcRes12Bit,             /* 12 bit resolution. */                             \
    adcPosSelAPORT0XCH0,     /* Select node BUS0XCH0 as posSel */                 \
    adcNegSelVSS,            /* Select VSS as negSel */                           \
    false,                   /* Single-ended input. */                            \
    false,                   /* PRS disabled. */                                  \
    false,                   /* Right adjust. */                                  \
    false,                   /* Deactivate conversion after one scan sequence. */ \
    false,                   /* No EM2 DMA wakeup from single FIFO DVL */         \
    false                    /* Discard new data on full FIFO. */                 \
  }
#endif

/*******************************************************************************
 *****************************   PROTOTYPES   **********************************
 ******************************************************************************/

/***************************************************************************//**
 * @brief
 *   Get a single conversion result.
 *
 * @note
 *   Check data valid flag before calling this function.
 *
 * @param[in] adc
 *   A pointer to the ADC peripheral register block.
 *
 * @return
 *   Single conversion data.
 ******************************************************************************/
__STATIC_INLINE uint32_t ADC_DataSingleGet(ADC_TypeDef *adc)
{
  return adc->SINGLEDATA;
}

/***************************************************************************//**
 * @brief
 *   Peek single conversion result.
 *
 * @note
 *   Check data valid flag before calling this function.
 *
 * @param[in] adc
 *   A pointer to the ADC peripheral register block.
 *
 * @return
 *   Single conversion data.
 ******************************************************************************/
__STATIC_INLINE uint32_t ADC_DataSinglePeek(ADC_TypeDef *adc)
{
  return adc->SINGLEDATAP;
}

/***************************************************************************//**
 * @brief
 *   Get a scan result.
 *
 * @note
 *   Check data valid flag before calling this function.
 *
 * @param[in] adc
 *   A pointer to the ADC peripheral register block.
 *
 * @return
 *   Scan conversion data.
 ******************************************************************************/
__STATIC_INLINE uint32_t ADC_DataScanGet(ADC_TypeDef *adc)
{
  return adc->SCANDATA;
}

/***************************************************************************//**
 * @brief
 *   Peek scan result.
 *
 * @note
 *   Check data valid flag before calling this function.
 *
 * @param[in] adc
 *   A pointer to the ADC peripheral register block.
 *
 * @return
 *   Scan conversion data.
 ******************************************************************************/
__STATIC_INLINE uint32_t ADC_DataScanPeek(ADC_TypeDef *adc)
{
  return adc->SCANDATAP;
}

#if defined(_ADC_SCANDATAX_MASK)
uint32_t ADC_DataIdScanGet(ADC_TypeDef *adc, uint32_t *scanId);
#endif

void ADC_Init(ADC_TypeDef *adc, const ADC_Init_TypeDef *init);
void ADC_Reset(ADC_TypeDef *adc);
void ADC_InitScan(ADC_TypeDef *adc, const ADC_InitScan_TypeDef *init);

#if defined(_ADC_SCANINPUTSEL_MASK)
void ADC_ScanInputClear(ADC_InitScan_TypeDef *scanInit);
uint32_t ADC_ScanSingleEndedInputAdd(ADC_InitScan_TypeDef *scanInit,
                                     ADC_ScanInputGroup_TypeDef inputGroup,
                                     ADC_PosSel_TypeDef singleEndedSel);
uint32_t ADC_ScanDifferentialInputAdd(ADC_InitScan_TypeDef *scanInit,
                                      ADC_ScanInputGroup_TypeDef inputGroup,
                                      ADC_PosSel_TypeDef posSel,
                                      ADC_ScanNegInput_TypeDef negInput);
#endif

void ADC_InitSingle(ADC_TypeDef *adc, const ADC_InitSingle_TypeDef *init);
uint8_t ADC_TimebaseCalc(uint32_t hfperFreq);
uint8_t ADC_PrescaleCalc(uint32_t adcFreq, uint32_t hfperFreq);

/***************************************************************************//**
 * @brief
 *   Clear one or more pending ADC interrupts.
 *
 * @param[in] adc
 *   A pointer to the ADC peripheral register block.
 *
 * @param[in] flags
 *   Pending ADC interrupt source to clear. Use a bitwise logic OR combination
 *   of valid interrupt flags for the ADC module (ADC_IF_nnn).
 ******************************************************************************/
__STATIC_INLINE void ADC_IntClear(ADC_TypeDef *adc, uint32_t flags)
{
  adc->IFC = flags;
}

/***************************************************************************//**
 * @brief
 *   Disable one or more ADC interrupts.
 *
 * @param[in] adc
 *   A pointer to the ADC peripheral register block.
 *
 * @param[in] flags
 *   ADC interrupt sources to disable. Use a bitwise logic OR combination of
 *   valid interrupt flags for the ADC module (ADC_IF_nnn).
 ******************************************************************************/
__STATIC_INLINE void ADC_IntDisable(ADC_TypeDef *adc, uint32_t flags)
{
  adc->IEN &= ~flags;
}

/***************************************************************************//**
 * @brief
 *   Enable one or more ADC interrupts.
 *
 * @note
 *   Depending on use, a pending interrupt may already be set prior to
 *   enabling the interrupt. Consider using ADC_IntClear() prior to enabling
 *   if the pending interrupt should be ignored.
 *
 * @param[in] adc
 *   A pointer to the ADC peripheral register block.
 *
 * @param[in] flags
 *   ADC interrupt sources to enable. Use a bitwise logic OR combination of
 *   valid interrupt flags for the ADC module (ADC_IF_nnn).
 ******************************************************************************/
__STATIC_INLINE void ADC_IntEnable(ADC_TypeDef *adc, uint32_t flags)
{
  adc->IEN |= flags;
}

/***************************************************************************//**
 * @brief
 *   Get pending ADC interrupt flags.
 *
 * @note
 *   This function does not clear event bits.
 *
 * @param[in] adc
 *   A pointer to the ADC peripheral register block.
 *
 * @return
 *   ADC interrupt sources pending. A bitwise logic OR combination of valid
 *   interrupt flags for the ADC module (ADC_IF_nnn).
 ******************************************************************************/
__STATIC_INLINE uint32_t ADC_IntGet(ADC_TypeDef *adc)
{
  return adc->IF;
}

/***************************************************************************//**
 * @brief
 *   Get enabled and pending ADC interrupt flags.
 *   Useful for handling more interrupt sources in the same interrupt handler.
 *
 * @param[in] adc
 *   A pointer to the ADC peripheral register block.
 *
 * @note
 *   This function does not clear interrupt flags.
 *
 * @return
 *   Pending and enabled ADC interrupt sources.
 *   The return value is the bitwise AND combination of
 *   - the OR combination of enabled interrupt sources in ADCx_IEN_nnn
 *     register (ADCx_IEN_nnn) and
 *   - the OR combination of valid interrupt flags of the ADC module
 *     (ADCx_IF_nnn).
 ******************************************************************************/
__STATIC_INLINE uint32_t ADC_IntGetEnabled(ADC_TypeDef *adc)
{
  uint32_t ien;

  /* Store ADCx->IEN in a temporary variable to define the explicit order
   * of volatile accesses. */
  ien = adc->IEN;

  /* Bitwise AND of pending and enabled interrupts */
  return adc->IF & ien;
}

/***************************************************************************//**
 * @brief
 *   Set one or more pending ADC interrupts from software.
 *
 * @param[in] adc
 *   A pointer to the ADC peripheral register block.
 *
 * @param[in] flags
 *   ADC interrupt sources to set to pending. Use a bitwise logic OR combination
 *   of valid interrupt flags for the ADC module (ADC_IF_nnn).
 ******************************************************************************/
__STATIC_INLINE void ADC_IntSet(ADC_TypeDef *adc, uint32_t flags)
{
  adc->IFS = flags;
}

/***************************************************************************//**
 * @brief
 *   Start scan sequence and/or single conversion.
 *
 * @param[in] adc
 *   A pointer to the ADC peripheral register block.
 *
 * @param[in] cmd
 *   A command indicating which type of sampling to start.
 ******************************************************************************/
__STATIC_INLINE void ADC_Start(ADC_TypeDef *adc, ADC_Start_TypeDef cmd)
{
  adc->CMD = (uint32_t)cmd;
}

/** @} (end addtogroup adc) */

#ifdef __cplusplus
}
#endif

#endif /* defined(ADC_COUNT) && (ADC_COUNT > 0) */
#endif /* EM_ADC_H */
