prudhvibelide/BLE-Fitness-Tracker/Firmware/gecko_sdk_4.4.4/platform/emlib/inc/em_lesense.h

/***************************************************************************//**
 * @file
 * @brief Low Energy Sensor (LESENSE) peripheral API
 *******************************************************************************
 * # License
 * <b>Copyright 2018 Silicon Laboratories Inc. www.silabs.com</b>
 *******************************************************************************
 *
 * SPDX-License-Identifier: Zlib
 *
 * The licensor of this software is Silicon Laboratories Inc.
 *
 * This software is provided 'as-is', without any express or implied
 * warranty. In no event will the authors be held liable for any damages
 * arising from the use of this software.
 *
 * Permission is granted to anyone to use this software for any purpose,
 * including commercial applications, and to alter it and redistribute it
 * freely, subject to the following restrictions:
 *
 * 1. The origin of this software must not be misrepresented; you must not
 *    claim that you wrote the original software. If you use this software
 *    in a product, an acknowledgment in the product documentation would be
 *    appreciated but is not required.
 * 2. Altered source versions must be plainly marked as such, and must not be
 *    misrepresented as being the original software.
 * 3. This notice may not be removed or altered from any source distribution.
 *
 ******************************************************************************/

#ifndef EM_LESENSE_H
#define EM_LESENSE_H

#include "em_device.h"

#if defined(LESENSE_COUNT) && (LESENSE_COUNT > 0)
#include <stdint.h>
#include <stdbool.h>

#ifdef __cplusplus
extern "C" {
#endif

/***************************************************************************//**
 * @addtogroup lesense
 * @{
 ******************************************************************************/

/** Number of decoder states supported by current device. */
#define LESENSE_NUM_DECODER_STATES   (_LESENSE_DECSTATE_DECSTATE_MASK + 1)
#if defined(_SILICON_LABS_32B_SERIES_2)
/** Number of ARCs supported by current device. Number of ARCS is the number of states times 2 */
#define LESENSE_NUM_ARCS   (LESENSE_NUM_DECODER_STATES << 1)
#endif
/** Number of LESENSE channels. */
#define LESENSE_NUM_CHANNELS         16

/*******************************************************************************
 ********************************   ENUMS   ************************************
 ******************************************************************************/

/** Clock divisors for controlling the prescaling factor of the period counter.
 *  Note: These enumeration values are used for different clock division
 *  related configuration parameters (hfPresc, lfPresc, pcPresc). */
typedef enum {
  lesenseClkDiv_1   = 0, /**< Divide clock by 1. */
  lesenseClkDiv_2   = 1, /**< Divide clock by 2. */
  lesenseClkDiv_4   = 2, /**< Divide clock by 4. */
  lesenseClkDiv_8   = 3, /**< Divide clock by 8. */
  lesenseClkDiv_16  = 4, /**< Divide clock by 16. */
  lesenseClkDiv_32  = 5, /**< Divide clock by 32. */
  lesenseClkDiv_64  = 6, /**< Divide clock by 64. */
  lesenseClkDiv_128 = 7  /**< Divide clock by 128. */
} LESENSE_ClkPresc_TypeDef;

/** Scan modes. */
#if defined(_SILICON_LABS_32B_SERIES_0) || defined(_SILICON_LABS_32B_SERIES_1)
typedef enum {
  /** New scan is started each time the period counter overflows. */
  lesenseScanStartPeriodic = LESENSE_CTRL_SCANMODE_PERIODIC,

  /** Single scan is performed when LESENSE_ScanStart() is called. */
  lesenseScanStartOneShot  = LESENSE_CTRL_SCANMODE_ONESHOT,

  /** New scan is triggered by pulse on PRS channel. */
  lesenseScanStartPRS      = LESENSE_CTRL_SCANMODE_PRS
} LESENSE_ScanMode_TypeDef;
#else
typedef enum {
  /** New scan is started each time the period counter overflows. */
  lesenseScanStartPeriodic = LESENSE_CFG_SCANMODE_PERIODIC,

  /** Single scan is performed when LESENSE_ScanStart() is called. */
  lesenseScanStartOneShot  = LESENSE_CFG_SCANMODE_ONESHOT,

  /** New scan is triggered by pulse on PRS channel. */
  lesenseScanStartPRS      = LESENSE_CFG_SCANMODE_PRS
} LESENSE_ScanMode_TypeDef;
#endif

/** PRS sources. */
/**  Note: These enumeration values are being used for different PRS related
 *  configuration parameters. */
typedef enum {
  lesensePRSCh0     = 0, /**< PRS channel 0. */
  lesensePRSCh1     = 1, /**< PRS channel 1. */
  lesensePRSCh2     = 2, /**< PRS channel 2. */
  lesensePRSCh3     = 3, /**< PRS channel 3. */
#if defined(LESENSE_CTRL_PRSSEL_PRSCH4) || defined(_SILICON_LABS_32B_SERIES_2)
  lesensePRSCh4     = 4, /**< PRS channel 4. */
#endif
#if defined(LESENSE_CTRL_PRSSEL_PRSCH5) || defined(_SILICON_LABS_32B_SERIES_2)
  lesensePRSCh5     = 5, /**< PRS channel 5. */
#endif
#if defined(LESENSE_CTRL_PRSSEL_PRSCH6) || defined(_SILICON_LABS_32B_SERIES_2)
  lesensePRSCh6     = 6, /**< PRS channel 6. */
#endif
#if defined(LESENSE_CTRL_PRSSEL_PRSCH7) || defined(_SILICON_LABS_32B_SERIES_2)
  lesensePRSCh7     = 7,  /**< PRS channel 7. */
#endif
#if defined(LESENSE_CTRL_PRSSEL_PRSCH8) || defined(_SILICON_LABS_32B_SERIES_2)
  lesensePRSCh8     = 8,  /**< PRS channel 8. */
#endif
#if defined(LESENSE_CTRL_PRSSEL_PRSCH9) || defined(_SILICON_LABS_32B_SERIES_2)
  lesensePRSCh9     = 9,  /**< PRS channel 9. */
#endif
#if defined(LESENSE_CTRL_PRSSEL_PRSCH10) || defined(_SILICON_LABS_32B_SERIES_2)
  lesensePRSCh10    = 10, /**< PRS channel 10.*/
#endif
#if defined(LESENSE_CTRL_PRSSEL_PRSCH11) || defined(_SILICON_LABS_32B_SERIES_2)
  lesensePRSCh11    = 11, /**< PRS channel 11.*/
#endif
} LESENSE_PRSSel_TypeDef;

#if defined(_SILICON_LABS_32B_SERIES_0) || defined(_SILICON_LABS_32B_SERIES_1)
/** Locations of the alternate excitation function. */
typedef enum {
  /** Alternate excitation is mapped to the LES_ALTEX pins. */
  lesenseAltExMapALTEX = _LESENSE_CTRL_ALTEXMAP_ALTEX,

#if defined(_LESENSE_CTRL_ALTEXMAP_ACMP)
  /** Alternate excitation is mapped to the pins of the other ACMP. */
  lesenseAltExMapACMP  = _LESENSE_CTRL_ALTEXMAP_ACMP,
#endif

#if defined(_LESENSE_CTRL_ALTEXMAP_CH)
  /** Alternative excitation is mapped to the pin of LESENSE channel
   * (X+8 mod 16) where X is the active channel. */
  lesenseAltExMapCH  = _LESENSE_CTRL_ALTEXMAP_CH,
#endif
} LESENSE_AltExMap_TypeDef;
#endif

#if defined(_SILICON_LABS_32B_SERIES_0) || defined(_SILICON_LABS_32B_SERIES_1)
/** Result buffer interrupt and DMA trigger levels. */
typedef enum {
  /** DMA and interrupt flags are set when the result buffer is half-full. */
  lesenseBufTrigHalf = LESENSE_CTRL_BUFIDL_HALFFULL,

  /** DMA and interrupt flags set when the result buffer is full. */
  lesenseBufTrigFull = LESENSE_CTRL_BUFIDL_FULL
} LESENSE_BufTrigLevel_TypeDef;
#endif

/** Modes of operation for DMA wakeup from EM2. */
#if defined(_SILICON_LABS_32B_SERIES_0) || defined(_SILICON_LABS_32B_SERIES_1)
typedef enum {
  /** No DMA wakeup from EM2. */
  lesenseDMAWakeUpDisable  = LESENSE_CTRL_DMAWU_DISABLE,

  /** DMA wakeup from EM2 when data is valid in the result buffer. */
  lesenseDMAWakeUpBufValid = LESENSE_CTRL_DMAWU_BUFDATAV,

  /** DMA wakeup from EM2 when the result buffer is full/half-full, depending on
   *  RESBIDL configuration in the LESENSE_CTRL register (selected by the
   *  resBufTrigLevel in LESENSE_ResBufTrigLevel_TypeDef descriptor structure). */
  lesenseDMAWakeUpBufLevel = LESENSE_CTRL_DMAWU_BUFLEVEL
} LESENSE_DMAWakeUp_TypeDef;
#else
typedef enum {
  /** No DMA wakeup from EM2. */
  lesenseDMAWakeUpDisable  = LESENSE_CFG_DMAWU_DISABLE,

  /** DMA wakeup from EM2. */
  lesenseDMAWakeUpEnable = LESENSE_CFG_DMAWU_ENABLE,
} LESENSE_DMAWakeUp_TypeDef;
#endif

#if defined(_SILICON_LABS_32B_SERIES_0) || defined(_SILICON_LABS_32B_SERIES_1)
/** Bias modes. */
typedef enum {
  /** Duty cycle bias module between low power and high accuracy mode. */
  lesenseBiasModeDutyCycle = LESENSE_BIASCTRL_BIASMODE_DUTYCYCLE,

  /** Bias module is always in high accuracy mode. */
  lesenseBiasModeHighAcc   = LESENSE_BIASCTRL_BIASMODE_HIGHACC,

  /** Bias module is controlled by EMU and not affected by the LESENSE. */
  lesenseBiasModeDontTouch = LESENSE_BIASCTRL_BIASMODE_DONTTOUCH
} LESENSE_BiasMode_TypeDef;
#endif

/** Scan configuration. */
#if defined(_SILICON_LABS_32B_SERIES_0) || defined(_SILICON_LABS_32B_SERIES_1)
typedef enum {
  /** Channel configuration registers (CHx_CONF) used are directly mapped to
   *  the channel number. */
  lesenseScanConfDirMap = LESENSE_CTRL_SCANCONF_DIRMAP,

  /** Channel configuration registers used are CHx+8_CONF for channels 0-7
   *  and CHx-8_CONF for channels 8-15. */
  lesenseScanConfInvMap = LESENSE_CTRL_SCANCONF_INVMAP,

  /** Channel configuration registers used toggles between CHX_SCANCONF and
   *  CHX+8_SCANCONF when channel x triggers. */
  lesenseScanConfToggle = LESENSE_CTRL_SCANCONF_TOGGLE,

  /** Decoder state defines the channel configuration register (CHx_CONF) to
   *  be used. */
  lesenseScanConfDecDef = LESENSE_CTRL_SCANCONF_DECDEF
} LESENSE_ScanConfSel_TypeDef;
#else
typedef enum {
  /** Channel configuration registers (CHx_CONF) used are directly mapped to
   *  the channel number. */
  lesenseScanConfDirMap = LESENSE_CFG_SCANCONF_DIRMAP,

  /** Channel configuration registers used are CHx+8_CONF for channels 0-7
   *  and CHx-8_CONF for channels 8-15. */
  lesenseScanConfInvMap = LESENSE_CFG_SCANCONF_INVMAP,

  /** Channel configuration registers used toggles between CHX_SCANCONF and
   *  CHX+8_SCANCONF when channel x triggers. */
  lesenseScanConfToggle = LESENSE_CFG_SCANCONF_TOGGLE,

  /** Decoder state defines the channel configuration register (CHx_CONF) to
   *  be used. */
  lesenseScanConfDecDef = LESENSE_CFG_SCANCONF_DECDEF
} LESENSE_ScanConfSel_TypeDef;
#endif

/** DAC CHx data control configuration. */
typedef enum {
  /** DAC channel x data is defined by the DAC_CHxDATA register.
  *  Note: this value could be used for both DAC Ch0 and Ch1. */
  lesenseDACIfData = _LESENSE_PERCTRL_DACCH0DATA_DACDATA,

#if defined(_LESENSE_PERCTRL_DACCH0DATA_ACMPTHRES)
  /** DAC channel x data is defined by the ACMPTHRES in LESENSE_CHx_INTERACT.
   *  Note: This value could be used for both DAC Ch0 and Ch1. */
  lesenseACMPThres = _LESENSE_PERCTRL_DACCH0DATA_ACMPTHRES,
#endif

#if defined(_LESENSE_PERCTRL_DACCH0DATA_THRES)
  /** DAC channel x data is defined by the THRES in LESENSE_CHx_INTERACT.
   *  Note: This value could be used for both DAC Ch0 and Ch1. */
  lesenseThres     = _LESENSE_PERCTRL_DACCH0DATA_THRES,
#endif
} LESENSE_ControlDACData_TypeDef;

#if defined(_LESENSE_PERCTRL_DACCH0CONV_MASK)
/** DAC channel x conversion mode configuration. */
typedef enum {
  /** LESENSE does not control the DAC channel x.
   *  Note: This value could be used for both DAC Ch0 and Ch1. */
  lesenseDACConvModeDisable    = _LESENSE_PERCTRL_DACCH0CONV_DISABLE,

  /** DAC channel x is driven in continuous mode.
   *  Note: This value could be used for both DAC Ch0 and Ch1. */
  lesenseDACConvModeContinuous = _LESENSE_PERCTRL_DACCH0CONV_CONTINUOUS,

  /** DAC channel x is driven in sample hold mode.
   *  Note: This value could be used for both DAC Ch0 and Ch1. */
  lesenseDACConvModeSampleHold = _LESENSE_PERCTRL_DACCH0CONV_SAMPLEHOLD,

  /** DAC channel x is driven in sample off mode.
   *  Note: This value could be used for both DAC Ch0 and Ch1. */
  lesenseDACConvModeSampleOff  = _LESENSE_PERCTRL_DACCH0CONV_SAMPLEOFF
} LESENSE_ControlDACConv_TypeDef;
#endif

#if defined(_LESENSE_PERCTRL_DACCH0OUT_MASK)
/** DAC channel x output mode configuration. */
typedef enum {
  /** DAC CHx output to pin and ACMP/ADC disabled.
   *  Note: This value could be used for both DAC Ch0 and Ch1. */
  lesenseDACOutModeDisable    = _LESENSE_PERCTRL_DACCH0OUT_DISABLE,

  /** DAC CHx output to pin enabled, output to ADC and ACMP disabled.
   *  Note: This value could be used for both DAC Ch0 and Ch1. */
  lesenseDACOutModePin        = _LESENSE_PERCTRL_DACCH0OUT_PIN,

  /** DAC CHx output to pin disabled, output to ADC and ACMP enabled.
   *  Note: This value could be used for both DAC Ch0 and Ch1. */
  lesenseDACOutModeADCACMP    = _LESENSE_PERCTRL_DACCH0OUT_ADCACMP,

  /** DAC CHx output to pin, ADC, and ACMP enabled.
   *  Note: This value could be used for both DAC Ch0 and Ch1. */
  lesenseDACOutModePinADCACMP = _LESENSE_PERCTRL_DACCH0OUT_PINADCACMP
} LESENSE_ControlDACOut_TypeDef;
#endif

#if defined(_LESENSE_PERCTRL_DACREF_MASK)
/**  DAC reference configuration. */
typedef enum {
  /** DAC uses VDD reference. */
  lesenseDACRefVdd     = LESENSE_PERCTRL_DACREF_VDD,

  /** DAC uses band gap reference. */
  lesenseDACRefBandGap = LESENSE_PERCTRL_DACREF_BANDGAP
} LESENSE_DACRef_TypeDef;
#endif

/** ACMPx control configuration. */
typedef enum {
  /** LESENSE does not control ACMPx.
   *  Note: This value could be used for both ACMP0 and ACMP1. */
#if defined(_SILICON_LABS_32B_SERIES_0) || defined(_SILICON_LABS_32B_SERIES_1)
  lesenseACMPModeDisable  = _LESENSE_PERCTRL_ACMP0MODE_DISABLE,
#endif

  /** LESENSE controls input mux of ACMPx.
   *  Note: This value could be used for both ACMP0 and ACMP1. */
  lesenseACMPModeMux      = _LESENSE_PERCTRL_ACMP0MODE_MUX,

  /** LESENSE controls input mux of and threshold value of ACMPx.
   *  Note: This value could be used for both ACMP0 and ACMP1. */
  lesenseACMPModeMuxThres = _LESENSE_PERCTRL_ACMP0MODE_MUXTHRES
} LESENSE_ControlACMP_TypeDef;

#if defined(_SILICON_LABS_32B_SERIES_0) || defined(_SILICON_LABS_32B_SERIES_1)
/** Warm up modes. ACMP and DAC duty cycle mode configuration. */
typedef enum {
  /** ACMPs and DACs are shut down when LESENSE is idle. */
  lesenseWarmupModeNormal   = LESENSE_PERCTRL_WARMUPMODE_NORMAL,

  /** ACMPs are kept powered up when LESENSE is idle. */
  lesenseWarmupModeACMP     = LESENSE_PERCTRL_WARMUPMODE_KEEPACMPWARM,

  /** DAC is kept powered up when LESENSE is idle. */
  lesenseWarmupModeDAC      = LESENSE_PERCTRL_WARMUPMODE_KEEPDACWARM,

  /** ACMPs and DAC are kept powered up when LESENSE is idle. */
  lesenseWarmupModeKeepWarm = LESENSE_PERCTRL_WARMUPMODE_KEEPACMPDACWARM
} LESENSE_WarmupMode_TypeDef;
#endif

/** Decoder input source configuration. */
#if defined(_SILICON_LABS_32B_SERIES_0) || defined(_SILICON_LABS_32B_SERIES_1)
typedef enum {
  /** SENSORSTATE register is used as input to the decoder. */
  lesenseDecInputSensorSt = LESENSE_DECCTRL_INPUT_SENSORSTATE,

  /** PRS channels are used as input to the decoder. */
  lesenseDecInputPRS      = LESENSE_DECCTRL_INPUT_PRS
} LESENSE_DecInput_TypeDef;
#else
/** Ocelot only provides SENSORSTATE as input for the decoder. */
#endif

/** Compare source selection for sensor sampling. */
typedef enum {
  /** Counter output will be used in comparison. */
#if defined(_SILICON_LABS_32B_SERIES_0) || defined(_SILICON_LABS_32B_SERIES_1)
  lesenseSampleModeCounter = 0x0 << _LESENSE_CH_INTERACT_SAMPLE_SHIFT,
#else
  lesenseSampleModeCounter = LESENSE_CH_INTERACT_SAMPLE_ACMPCOUNT,
#endif

  /** ACMP output will be used in comparison. */
  lesenseSampleModeACMP    = LESENSE_CH_INTERACT_SAMPLE_ACMP,

#if defined(LESENSE_CH_INTERACT_SAMPLE_ADC)
  /** ADC output will be used in comparison. */
  lesenseSampleModeADC     = LESENSE_CH_INTERACT_SAMPLE_ADC,

  /** Differential ADC output will be used in comparison. */
  lesenseSampleModeADCDiff = LESENSE_CH_INTERACT_SAMPLE_ADCDIFF,
#endif
} LESENSE_ChSampleMode_TypeDef;

/** Interrupt generation setup for CHx interrupt flag. */
typedef enum {
  /** No interrupt is generated. */
  lesenseSetIntNone      = LESENSE_CH_INTERACT_SETIF_NONE,

  /** Set interrupt flag if the sensor triggers. */
  lesenseSetIntLevel     = LESENSE_CH_INTERACT_SETIF_LEVEL,

  /** Set interrupt flag on positive edge of the sensor state. */
  lesenseSetIntPosEdge   = LESENSE_CH_INTERACT_SETIF_POSEDGE,

  /** Set interrupt flag on negative edge of the sensor state. */
  lesenseSetIntNegEdge   = LESENSE_CH_INTERACT_SETIF_NEGEDGE,

#if defined(LESENSE_CH_INTERACT_SETIF_BOTHEDGES)
  /** Set interrupt flag on both edges of the sensor state. */
  lesenseSetIntBothEdges = LESENSE_CH_INTERACT_SETIF_BOTHEDGES
#endif
} LESENSE_ChIntMode_TypeDef;

/** Channel pin mode for the excitation phase of the scan sequence. */
typedef enum {
  /** Channel pin is disabled. */
  lesenseChPinExDis    = LESENSE_CH_INTERACT_EXMODE_DISABLE,

  /** Channel pin is configured as push-pull, driven HIGH. */
  lesenseChPinExHigh   = LESENSE_CH_INTERACT_EXMODE_HIGH,

  /** Channel pin is configured as push-pull, driven LOW. */
  lesenseChPinExLow    = LESENSE_CH_INTERACT_EXMODE_LOW,

  /** DAC output (only available on channel 0, 1, 2, 3, 12, 13, 14 and 15) */
  lesenseChPinExDACOut = LESENSE_CH_INTERACT_EXMODE_DACOUT
} LESENSE_ChPinExMode_TypeDef;

/** Channel pin mode for the idle phase of scan sequence. */
#if defined(_SILICON_LABS_32B_SERIES_0) || defined(_SILICON_LABS_32B_SERIES_1)
typedef enum {
  /** Channel pin is disabled in idle phase.
   *  Note: This value could be used for all channels. */
  lesenseChPinIdleDis    = _LESENSE_IDLECONF_CH0_DISABLE,

  /** Channel pin is configured as push-pull, driven HIGH in idle phase.
   *  Note: This value could be used for all channels. */
  lesenseChPinIdleHigh   = _LESENSE_IDLECONF_CH0_HIGH,

  /** Channel pin is configured as push-pull, driven LOW in idle phase.
   *  Note: This value could be used for all channels. */
  lesenseChPinIdleLow    = _LESENSE_IDLECONF_CH0_LOW,

#if defined(_LESENSE_IDLECONF_CH0_DAC)
  /** Channel pin is connected to DAC output in idle phase.
   *  Note: This value could be used for all channels. */
  lesenseChPinIdleDACC   = _LESENSE_IDLECONF_CH0_DAC
#else
  /** Channel pin is connected to DAC CH0 output in idle phase.
   *  Note: Only applies to channel 0, 1, 2, 3. */
  lesenseChPinIdleDACCh0 = _LESENSE_IDLECONF_CH0_DACCH0,

  /** Channel pin is connected to DAC CH1 output in idle phase.
   *  Note: Only applies to channel 12, 13, 14, 15. */
  lesenseChPinIdleDACCh1 = _LESENSE_IDLECONF_CH12_DACCH1,
#endif
} LESENSE_ChPinIdleMode_TypeDef;
#else
typedef enum {
  /** Channel pin is disabled in idle phase.
   *  Note: This value could be used for all channels. */
  lesenseChPinIdleDis = _LESENSE_IDLECONF_CHIDLE0_DISABLE,

  /** Channel pin is configured as push-pull, driven HIGH in idle phase.
   *  Note: This value could be used for all channels. */
  lesenseChPinIdleHigh   = _LESENSE_IDLECONF_CHIDLE0_HIGH,

  /** Channel pin is configured as push-pull, driven LOW in idle phase.
   *  Note: This value could be used for all channels. */
  lesenseChPinIdleLow    = _LESENSE_IDLECONF_CHIDLE0_LOW,

  /** Channel pin is connected to DAC output in idle phase.
   *  Note: This value could be used for all channels. */
  lesenseChPinIdleDACC   = _LESENSE_IDLECONF_CHIDLE0_DAC
} LESENSE_ChPinIdleMode_TypeDef;
#endif

/** Clock used for excitation and sample delay timing. */
typedef enum {
  /** LFACLK (LF clock) is used. */
  lesenseClkLF = _LESENSE_CH_INTERACT_EXCLK_LFACLK,

  /** AUXHFRCO (HF clock) is used. */
  lesenseClkHF = _LESENSE_CH_INTERACT_EXCLK_AUXHFRCO
} LESENSE_ChClk_TypeDef;

/** Compare modes for counter comparison. */
#if defined(_SILICON_LABS_32B_SERIES_0) || defined(_SILICON_LABS_32B_SERIES_1)
typedef enum {
  /** Comparison evaluates to 1 if sensor data is less than the counter
   *  threshold, or if ACMP output is 0. */
  lesenseCompModeLess        = LESENSE_CH_EVAL_COMP_LESS,

  /** Comparison evaluates to 1 if sensor data is greater than, or equal to
   *  the counter threshold, or if the ACMP output is 1. */
  lesenseCompModeGreaterOrEq = LESENSE_CH_EVAL_COMP_GE
} LESENSE_ChCompMode_TypeDef;
#else
typedef enum {
  /** Comparison evaluates to 1 if sensor data is less than the counter
   *  threshold, or if ACMP output is 0. */
  lesenseCompModeLess        = LESENSE_CH_EVALCFG_COMP_LESS,

  /** Comparison evaluates to 1 if sensor data is greater than, or equal to
   *  the counter threshold, or if the ACMP output is 1. */
  lesenseCompModeGreaterOrEq = LESENSE_CH_EVALCFG_COMP_GE
} LESENSE_ChCompMode_TypeDef;
#endif

/** Mode of Storing of Sensor Sample in Result Buffer. */
#if defined(_SILICON_LABS_32B_SERIES_0)
typedef enum {
  /** Nothing will be stored in the result buffer. */
  lesenseStoreSampleDisable = _LESENSE_CH_EVAL_STRSAMPLE_DEFAULT,

  /** The sensor sample data will be stored in the result buffer. */
  lesenseStoreSampleData = _LESENSE_CH_EVAL_STRSAMPLE_MASK >> _LESENSE_CH_EVAL_STRSAMPLE_SHIFT
} LESENSE_StoreSample_TypeDef;
#elif defined (_SILICON_LABS_32B_SERIES_1)
typedef enum {
  /** Nothing will be stored in the result buffer. */
  lesenseStoreSampleDisable = _LESENSE_CH_EVAL_STRSAMPLE_DISABLE,

  /** The sensor sample data will be stored in the result buffer. */
  lesenseStoreSampleData = _LESENSE_CH_EVAL_STRSAMPLE_DATA,

  /** The data source (i.e. the channel) will be stored alongside the sensor
   *  sample data. */
  lesenseStoreSampleDataSrc = _LESENSE_CH_EVAL_STRSAMPLE_DATASRC
} LESENSE_StoreSample_TypeDef;
#else
typedef enum {
  /** Nothing will be stored in the result buffer. */
  lesenseStoreSampleDisable = _LESENSE_CH_EVALCFG_STRSAMPLE_DISABLE,

  /** The sensor sample data will be stored in the result buffer. */
  lesenseStoreSampleData = _LESENSE_CH_EVALCFG_STRSAMPLE_DATA,

  /** The data source (i.e. the channel) will be stored alongside the sensor
   *  sample data. */
  lesenseStoreSampleDataSrc = _LESENSE_CH_EVALCFG_STRSAMPLE_DATASRC
} LESENSE_StoreSample_TypeDef;
#endif

/** Sensor evaluation modes. */
#if defined(_SILICON_LABS_32B_SERIES_0) || defined(_SILICON_LABS_32B_SERIES_1)
#if defined(_LESENSE_CH_EVAL_MODE_MASK)
typedef enum {
  /** Threshold comparison evaluation mode. In this mode, sensor data
   *  is compared to the configured threshold value. Two possible comparison
   *  operators can be used on sensor data, either >= (GE) or < (LT).
   *  Which operator to use is given using the
   *  @ref LESENSE_ChDesc_TypeDef::compMode member. */
  lesenseEvalModeThreshold        = _LESENSE_CH_EVAL_MODE_THRES,

  /** Sliding window evaluation mode. In this mode, sensor data is
   *  evaluated against upper and lower limits of a window range. The
   *  windows range is defined by a base value and a window size. */
  lesenseEvalModeSlidingWindow    = _LESENSE_CH_EVAL_MODE_SLIDINGWIN,

  /** Step detection evaluation mode. In this mode, the sensor data is compared
   *  to the sensor data from the previous measurement. Sensor evaluation
   *  will result in a "1" if the difference between current measurement
   *  and previous one is greater than a configurable "step size". If the
   *  difference is less than the configured step size then sensor
   *  evaluation will result in a "0". */
  lesenseEvalModeStepDetection    = _LESENSE_CH_EVAL_MODE_STEPDET,
} LESENSE_ChEvalMode_TypeDef;
#endif
#else
typedef enum {
  /** Threshold comparison evaluation mode. In this mode, sensor data
   *  is compared to the configured threshold value. Two possible comparison
   *  operators can be used on sensor data, either >= (GE) or < (LT).
   *  Which operator to use is given using the
   *  @ref LESENSE_ChDesc_TypeDef::compMode member. */
  lesenseEvalModeThreshold        = _LESENSE_CH_EVALCFG_MODE_THRES,

  /** Sliding window evaluation mode. In this mode, sensor data is
   *  evaluated against upper and lower limits of a window range. The
   *  windows range is defined by a base value and a window size. */
  lesenseEvalModeSlidingWindow    = _LESENSE_CH_EVALCFG_MODE_SLIDINGWIN,

  /** Step detection evaluation mode. In this mode, the sensor data is compared
   *  to the sensor data from the previous measurement. Sensor evaluation
   *  will result in a "1" if the difference between current measurement
   *  and previous one is greater than a configurable "step size". If the
   *  difference is less than the configured step size then sensor
   *  evaluation will result in a "0". */
  lesenseEvalModeStepDetection    = _LESENSE_CH_EVALCFG_MODE_STEPDET,
} LESENSE_ChEvalMode_TypeDef;
#endif

#if defined(_SILICON_LABS_32B_SERIES_0) || defined(_SILICON_LABS_32B_SERIES_1)
/** Idle phase configuration of the alternate excitation channels. */
typedef enum {
  /** ALTEX output is disabled in idle phase.
   *  Note: This value could be used for all the alternate excitation channels. */
  lesenseAltExPinIdleDis  = _LESENSE_ALTEXCONF_IDLECONF0_DISABLE,

  /** ALTEX output is high in idle phase.
   *  Note: This value could be used for all the alternate excitation channels. */
  lesenseAltExPinIdleHigh = _LESENSE_ALTEXCONF_IDLECONF0_HIGH,

  /** ALTEX output is low in idle phase.
   *  Note: This value could be used for all the alternate excitation channels. */
  lesenseAltExPinIdleLow  = _LESENSE_ALTEXCONF_IDLECONF0_LOW
} LESENSE_AltExPinIdle_TypeDef;
#endif

/** Transition action modes. */
#if defined(_SILICON_LABS_32B_SERIES_0) || defined(_SILICON_LABS_32B_SERIES_1)
typedef enum {
  /** No PRS pulses generated (if PRSCOUNT == 0).
   *  Do not count (if PRSCOUNT == 1). */
  lesenseTransActNone        = LESENSE_ST_TCONFA_PRSACT_NONE,

  /** Generate pulse on LESPRS0 (if PRSCOUNT == 0). */
  lesenseTransActPRS0        = LESENSE_ST_TCONFA_PRSACT_PRS0,

  /** Generate pulse on LESPRS1 (if PRSCOUNT == 0). */
  lesenseTransActPRS1        = LESENSE_ST_TCONFA_PRSACT_PRS1,

  /** Generate pulse on LESPRS0 and LESPRS1 (if PRSCOUNT == 0). */
  lesenseTransActPRS01       = LESENSE_ST_TCONFA_PRSACT_PRS01,

  /** Generate pulse on LESPRS2 (for both PRSCOUNT == 0 and PRSCOUNT == 1). */
  lesenseTransActPRS2        = LESENSE_ST_TCONFA_PRSACT_PRS2,

  /** Generate pulse on LESPRS0 and LESPRS2 (if PRSCOUNT == 0). */
  lesenseTransActPRS02       = LESENSE_ST_TCONFA_PRSACT_PRS02,

  /** Generate pulse on LESPRS1 and LESPRS2 (if PRSCOUNT == 0). */
  lesenseTransActPRS12       = LESENSE_ST_TCONFA_PRSACT_PRS12,

  /** Generate pulse on LESPRS0, LESPRS1 and LESPRS2  (if PRSCOUNT == 0). */
  lesenseTransActPRS012      = LESENSE_ST_TCONFA_PRSACT_PRS012,

  /** Count up (if PRSCOUNT == 1). */
  lesenseTransActUp          = LESENSE_ST_TCONFA_PRSACT_UP,

  /** Count down (if PRSCOUNT == 1). */
  lesenseTransActDown        = LESENSE_ST_TCONFA_PRSACT_DOWN,

  /** Count up and generate pulse on LESPRS2 (if PRSCOUNT == 1). */
  lesenseTransActUpAndPRS2   = LESENSE_ST_TCONFA_PRSACT_UPANDPRS2,

  /** Count down and generate pulse on LESPRS2 (if PRSCOUNT == 1). */
  lesenseTransActDownAndPRS2 = LESENSE_ST_TCONFA_PRSACT_DOWNANDPRS2
} LESENSE_StTransAct_TypeDef;
#else
typedef enum {
  /** No PRS pulses generated (if PRSCOUNT == 0).
   *  Do not count (if PRSCOUNT == 1). */
  lesenseTransActNone        = LESENSE_ST_ARC_PRSACT_NONE,

  /** Generate pulse on LESPRS0 (if PRSCOUNT == 0). */
  lesenseTransActPRS0        = LESENSE_ST_ARC_PRSACT_PRS0,

  /** Generate pulse on LESPRS1 (if PRSCOUNT == 0). */
  lesenseTransActPRS1        = LESENSE_ST_ARC_PRSACT_PRS1,

  /** Generate pulse on LESPRS0 and LESPRS1 (if PRSCOUNT == 0). */
  lesenseTransActPRS01       = LESENSE_ST_ARC_PRSACT_PRS01,

  /** Generate pulse on LESPRS2 (for both PRSCOUNT == 0 and PRSCOUNT == 1). */
  lesenseTransActPRS2        = LESENSE_ST_ARC_PRSACT_PRS2,

  /** Generate pulse on LESPRS0 and LESPRS2 (if PRSCOUNT == 0). */
  lesenseTransActPRS02       = LESENSE_ST_ARC_PRSACT_PRS02,

  /** Generate pulse on LESPRS1 and LESPRS2 (if PRSCOUNT == 0). */
  lesenseTransActPRS12       = LESENSE_ST_ARC_PRSACT_PRS12,

  /** Generate pulse on LESPRS0, LESPRS1 and LESPRS2  (if PRSCOUNT == 0). */
  lesenseTransActPRS012      = LESENSE_ST_ARC_PRSACT_PRS012,

  /** Count up (if PRSCOUNT == 1). */
  lesenseTransActUp          = LESENSE_ST_ARC_PRSACT_UP,

  /** Count down (if PRSCOUNT == 1). */
  lesenseTransActDown        = LESENSE_ST_ARC_PRSACT_DOWN,

  /** Count up and generate pulse on LESPRS2 (if PRSCOUNT == 1). */
  lesenseTransActUpAndPRS2   = LESENSE_ST_ARC_PRSACT_UPANDPRS2,

  /** Count down and generate pulse on LESPRS2 (if PRSCOUNT == 1). */
  lesenseTransActDownAndPRS2 = LESENSE_ST_ARC_PRSACT_DOWNANDPRS2
} LESENSE_StTransAct_TypeDef;
#endif

/*******************************************************************************
 *******************************   STRUCTS   ***********************************
 ******************************************************************************/

/** Core control (LESENSE_CTRL/CFG) descriptor structure. */
typedef struct {
  /** Select scan start mode to control how the scan start is being triggered.*/
  LESENSE_ScanMode_TypeDef     scanStart;

  /** Select PRS source for scan start if scanMode is set to lesensePrsPulse. */
  LESENSE_PRSSel_TypeDef       prsSel;

  /** Select scan configuration register usage strategy. */
  LESENSE_ScanConfSel_TypeDef  scanConfSel;

  /** Set to true to invert ACMP0 output. */
  bool                         invACMP0;

  /** Set to true to invert ACMP1 output. */
  bool                         invACMP1;

  /** Set to true to sample both ACMPs simultaneously. */
  bool                         dualSample;

  /** Set to true in order to store SCANRES in the RAM (accessible via RESDATA)
   *  after each scan. */
  bool                         storeScanRes;

#if defined(_SILICON_LABS_32B_SERIES_0) || defined(_SILICON_LABS_32B_SERIES_1)
  /** Set to true in order to always make LESENSE write to the result buffer,
   *  even if it is full. */
  bool                         bufOverWr;
#endif

#if defined(_SILICON_LABS_32B_SERIES_0) || defined(_SILICON_LABS_32B_SERIES_1)
  /** Select trigger conditions for the interrupt and DMA. */
  LESENSE_BufTrigLevel_TypeDef bufTrigLevel;
#else
  /** Select result FIFO interrupt and DMA trigger level.*/
  uint8_t                      fifoTrigLevel;
#endif

  /** Configure trigger condition for the DMA wakeup from EM2. */
  LESENSE_DMAWakeUp_TypeDef    wakeupOnDMA;

#if defined(_SILICON_LABS_32B_SERIES_0) || defined(_SILICON_LABS_32B_SERIES_1)
  /** Select bias mode. */
  LESENSE_BiasMode_TypeDef     biasMode;
#endif

  /** Set to true to keep LESENSE running in the debug mode. */
  bool                         debugRun;
} LESENSE_CoreCtrlDesc_TypeDef;

/** Default configuration for LESENSE_CtrlDesc_TypeDef structure. */
#if defined(_SILICON_LABS_32B_SERIES_0) || defined(_SILICON_LABS_32B_SERIES_1)
#define LESENSE_CORECTRL_DESC_DEFAULT                                                               \
  {                                                                                                 \
    lesenseScanStartPeriodic,/* Start new scan each time the period counter overflows. */           \
    lesensePRSCh0,           /* Default PRS channel is selected. */                                 \
    lesenseScanConfDirMap,   /* Direct mapping SCANCONF register usage strategy. */                 \
    false,                   /* Do not invert ACMP0 output. */                                      \
    false,                   /* Do not invert ACMP1 output. */                                      \
    false,                   /* Disable dual sampling. */                                           \
    true,                    /* Store scan result after each scan. */                               \
    true,                    /* Overwrite result buffer register even if it is full. */             \
    lesenseBufTrigHalf,      /* Trigger interrupt and DMA request if result buffer is half full. */ \
    lesenseDMAWakeUpDisable, /* Do not wake up on DMA from EM2. */                                  \
    lesenseBiasModeDontTouch,/* Do not touch bias configuration. */                                 \
    true                     /* Keep LESENSE running in debug mode. */                              \
  }
#else
#define LESENSE_CORECTRL_DESC_DEFAULT                                                     \
  {                                                                                       \
    lesenseScanStartPeriodic,/* Start new scan each time the period counter overflows. */ \
    lesensePRSCh0,           /* Default PRS channel is selected. */                       \
    lesenseScanConfDirMap,   /* Direct mapping SCANCONF register usage strategy. */       \
    false,                   /* Do not invert ACMP0 output. */                            \
    false,                   /* Do not invert ACMP1 output. */                            \
    false,                   /* Disable dual sampling. */                                 \
    true,                    /* Store scan result after each scan. */                     \
    15u,                     /* Default value for the FIFO trigger level */               \
    lesenseDMAWakeUpDisable, /* Do not wake up on DMA from EM2. */                        \
    true                     /* Keep LESENSE running in debug mode. */                    \
  }
#endif

/** LESENSE timing control descriptor structure. */
typedef struct {
  /** Set number of LFACLK cycles to delay sensor interaction on
   *  each channel. Valid range: 0-3 (2 bit). */
  uint8_t startDelay;

  /**
   * Set to true do delay startup of AUXHFRCO until the system enters
   * excite phase. This will reduce the time AUXHFRCO is enabled and
   * reduce power usage. */
  bool    delayAuxStartup;
} LESENSE_TimeCtrlDesc_TypeDef;

/** Default configuration for LESENSE_TimeCtrlDesc_TypeDef structure. */
#define LESENSE_TIMECTRL_DESC_DEFAULT              \
  {                                                \
    0U, /* No sensor interaction delay. */         \
    false /* Do not delay the AUXHFRCO startup. */ \
  }

/** LESENSE peripheral control descriptor structure. */
typedef struct {
  /** Configure DAC channel 0 data control. */
  LESENSE_ControlDACData_TypeDef dacCh0Data;

#if defined(_LESENSE_PERCTRL_DACCH0CONV_MASK)
  /** Configure how LESENSE controls conversion on DAC channel 0. */
  LESENSE_ControlDACConv_TypeDef dacCh0ConvMode;
#endif

#if defined(_LESENSE_PERCTRL_DACCH0OUT_MASK)
  /** Configure how LESENSE controls output on DAC channel 0. */
  LESENSE_ControlDACOut_TypeDef  dacCh0OutMode;
#endif

#if defined(_SILICON_LABS_32B_SERIES_0) || defined(_SILICON_LABS_32B_SERIES_1)
  /** Configure DAC channel 1 data control. */
  LESENSE_ControlDACData_TypeDef dacCh1Data;
#endif

#if defined(_LESENSE_PERCTRL_DACCH1CONV_MASK)
  /** Configure how LESENSE controls conversion on DAC channel 1. */
  LESENSE_ControlDACConv_TypeDef dacCh1ConvMode;
#endif

#if defined(_LESENSE_PERCTRL_DACCH1OUT_MASK)
  /** Configure how LESENSE controls output on DAC channel 1. */
  LESENSE_ControlDACOut_TypeDef  dacCh1OutMode;
#endif

#if defined(_LESENSE_PERCTRL_DACPRESC_MASK)
  /** Configure the prescaling factor for the LESENSE - DAC interface.
   *  Valid range: 0-31 (5-bit). */
  uint8_t                        dacPresc;
#endif

#if defined(_LESENSE_PERCTRL_DACREF_MASK)
  /** Configure the DAC reference to be used. Set to #lesenseDACRefVdd to use
   *  VDD and set to #lesenseDACRefBandGap to use band gap as reference. */
  LESENSE_DACRef_TypeDef         dacRef;
#endif

  /** Configure how LESENSE controls ACMP 0. */
  LESENSE_ControlACMP_TypeDef    acmp0Mode;

  /** Configure how LESENSE controls ACMP 1. */
  LESENSE_ControlACMP_TypeDef    acmp1Mode;

#if defined(_SILICON_LABS_32B_SERIES_0) || defined(_SILICON_LABS_32B_SERIES_1)
  /** Configure how LESENSE controls ACMPs and DAC in idle mode. */
  LESENSE_WarmupMode_TypeDef     warmupMode;
#endif

#if defined(_LESENSE_PERCTRL_DACCONVTRIG_MASK)
  /** When set to true the DAC is only enabled once for each scan. When
   *  set to false the DAC is enabled before every channel measurement. */
  bool                           dacScan;
#endif

#if defined(_LESENSE_PERCTRL_DACSTARTUP_MASK)
  /** When set to true the DAC is started a half clock cycle before sensor
  *  interaction starts. When set to false, a full clock cycle is used. */
  bool                           dacStartupHalf;
#endif

#if defined(_LESENSE_PERCTRL_DACCH0EN_MASK)
  /** When set to true, LESENSE controls DAC channel 0. */
  bool                           dacCh0En;
#endif

#if defined(_LESENSE_PERCTRL_DACCH1EN_MASK)
  /** When set to true, LESENSE controls DAC channel 1. */
  bool                           dacCh1En;
#endif
} LESENSE_PerCtrlDesc_TypeDef;

/** Default configuration for LESENSE_PerCtrl_TypeDef structure. */
#if defined(_SILICON_LABS_32B_SERIES_0)
#define LESENSE_PERCTRL_DESC_DEFAULT                                                                 \
  {                                                                                                  \
    lesenseDACIfData,         /* DAC channel 0 data is defined by DAC_CH0DATA register */            \
    lesenseDACConvModeDisable,/* LESENSE does not control DAC CH0. */                                \
    lesenseDACOutModeDisable, /* DAC channel 0 output to pin disabled. */                            \
    lesenseDACIfData,         /* DAC channel 1 data is defined by DAC_CH1DATA register */            \
    lesenseDACConvModeDisable,/* LESENSE does not control DAC CH1. */                                \
    lesenseDACOutModeDisable, /* DAC channel 1 output to pin disabled. */                            \
    0U,                       /* DAC prescaling factor of 1 (0+1). */                                \
    lesenseDACRefVdd,         /* DAC uses VDD reference. */                                          \
    lesenseACMPModeMuxThres,  /* LESENSE controls input mux and threshold value of ACMP0.         */ \
    lesenseACMPModeMuxThres,  /* LESENSE controls input mux and threshold value of ACMP1.         */ \
    lesenseWarmupModeKeepWarm /* Keep both ACMPs and DAC powered up when LESENSE is idle. */         \
  }
#elif defined(_SILICON_LABS_32B_SERIES_1)
#define LESENSE_PERCTRL_DESC_DEFAULT                                                                 \
  {                                                                                                  \
    lesenseDACIfData,         /* DAC channel 0 data is defined by DAC_CH0DATA register. */           \
    lesenseDACIfData,         /* DAC channel 1 data is defined by DAC_CH1DATA register. */           \
    lesenseACMPModeMuxThres,  /* LESENSE controls input mux and threshold value of ACMP0.         */ \
    lesenseACMPModeMuxThres,  /* LESENSE controls input mux and threshold value of ACMP1.         */ \
    lesenseWarmupModeKeepWarm,/* Keep both ACMPs and DAC powered up when LESENSE is idle.     */     \
    false,                    /* DAC is enabled for before every channel measurement. */             \
    false,                    /* DAC is enabled a full clock cycle before sensor interaction */      \
    false,                    /* LESENSE does not control DAC channel 0. */                          \
    false                     /* LESENSE does not control DAC channel 1. */                          \
  }
#else
#define LESENSE_PERCTRL_DESC_DEFAULT                                                                 \
  {                                                                                                  \
    lesenseDACIfData,         /* DAC channel 0 data is defined by DAC_CH0DATA register. */           \
    lesenseACMPModeMuxThres,  /* LESENSE controls input mux and threshold value of ACMP0.         */ \
    lesenseACMPModeMuxThres,  /* LESENSE controls input mux and threshold value of ACMP1.         */ \
    false,                    /* DAC is enabled for before every channel measurement. */             \
    false,                    /* DAC is enabled a full clock cycle before sensor interaction */      \
  }
#endif

/** LESENSE decoder control descriptor structure. */
typedef struct {
#if defined(_SILICON_LABS_32B_SERIES_0) || defined(_SILICON_LABS_32B_SERIES_1)
  /** Select input to the LESENSE decoder. */
  LESENSE_DecInput_TypeDef decInput;

  /** Initial state of the LESENSE decoder. */
  uint32_t                 initState;
#endif

  /** Set to enable decoder to check the present state in addition
   *  to the states defined in TCONF. */
  bool                     chkState;

  /** When set, a transition from state x in decoder will set the interrupt flag
   *  CHx. */
  bool                     intMap;

  /** Set to enable hysteresis in decoder for suppressing the changes on PRS
   *  channel 0. */
  bool                     hystPRS0;

  /** Set to enable hysteresis in decoder for suppressing the changes on PRS
   *  channel 1. */
  bool                     hystPRS1;

  /** Set to enable hysteresis in decoder for suppressing the changes on PRS
   *  channel 2. */
  bool                     hystPRS2;

  /** Set to enable hysteresis in decoder for suppressing the interrupt
   *  requests. */
  bool                     hystIRQ;

  /** Set to enable count mode on decoder PRS channels 0 and 1 to produce
   *  outputs which can be used by a PCNT to count up or down. */
  bool                     prsCount;

#if defined(_SILICON_LABS_32B_SERIES_0) || defined(_SILICON_LABS_32B_SERIES_1)
  /** Select PRS channel input for bit 0 of LESENSE decoder. */
  LESENSE_PRSSel_TypeDef   prsChSel0;

  /** Select PRS channel input for bit 1 of LESENSE decoder. */
  LESENSE_PRSSel_TypeDef   prsChSel1;

  /** Select PRS channel input for bit 2 of LESENSE decoder. */
  LESENSE_PRSSel_TypeDef   prsChSel2;

  /** Select PRS channel input for bit 3 of LESENSE decoder. */
  LESENSE_PRSSel_TypeDef   prsChSel3;
#endif
} LESENSE_DecCtrlDesc_TypeDef;

/** Default configuration for LESENSE_PerCtrl_TypeDef structure. */
#if defined(_SILICON_LABS_32B_SERIES_0) || defined(_SILICON_LABS_32B_SERIES_1)
#define LESENSE_DECCTRL_DESC_DEFAULT                                                         \
  {                                                                                          \
    lesenseDecInputSensorSt, /* SENSORSTATE register is used as input to decoder.         */ \
    0U,                      /* State 0 is the initial state of decoder. */                  \
    false,                   /* Disable check of current state. */                           \
    true,                    /* Enable channel x % 16 interrupt on state x change. */        \
    true,                    /* Enable decoder hysteresis on PRS0 output. */                 \
    true,                    /* Enable decoder hysteresis on PRS1 output. */                 \
    true,                    /* Enable decoder hysteresis on PRS2 output. */                 \
    true,                    /* Enable decoder hysteresis on PRS3 output. */                 \
    false,                   /* Disable count mode on decoder PRS channels 0 and 1*/         \
    lesensePRSCh0,           /* PRS Channel 0 as input for bit 0 of LESENSE decoder. */      \
    lesensePRSCh1,           /* PRS Channel 1 as input for bit 1 of LESENSE decoder. */      \
    lesensePRSCh2,           /* PRS Channel 2 as input for bit 2 of LESENSE decoder. */      \
    lesensePRSCh3,           /* PRS Channel 3 as input for bit 3 of LESENSE decoder. */      \
  }
#else
#define LESENSE_DECCTRL_DESC_DEFAULT                                                  \
  {                                                                                   \
    false,                   /* Disable check of current state. */                    \
    true,                    /* Enable channel x % 16 interrupt on state x change. */ \
    true,                    /* Enable decoder hysteresis on PRS0 output. */          \
    true,                    /* Enable decoder hysteresis on PRS1 output. */          \
    true,                    /* Enable decoder hysteresis on PRS2 output. */          \
    true,                    /* Enable decoder hysteresis on PRS3 output. */          \
    false,                   /* Disable count mode on decoder PRS channels 0 and 1*/  \
  }
#endif

/** LESENSE module initialization structure. */
typedef struct {
  /** LESENSE core configuration parameters. */
  LESENSE_CoreCtrlDesc_TypeDef coreCtrl;

  /** LESENSE timing configuration parameters. */
  LESENSE_TimeCtrlDesc_TypeDef timeCtrl;

  /** LESENSE peripheral configuration parameters. */
  LESENSE_PerCtrlDesc_TypeDef  perCtrl;

  /** LESENSE decoder configuration parameters. */
  LESENSE_DecCtrlDesc_TypeDef  decCtrl;
} LESENSE_Init_TypeDef;

/** Default configuration for LESENSE_Init_TypeDef structure. */
#define LESENSE_INIT_DEFAULT                                                                \
  {                                                                                         \
    .coreCtrl = LESENSE_CORECTRL_DESC_DEFAULT, /* Default core control parameters. */       \
    .timeCtrl = LESENSE_TIMECTRL_DESC_DEFAULT, /* Default time control parameters. */       \
    .perCtrl  = LESENSE_PERCTRL_DESC_DEFAULT,  /* Default peripheral control parameters. */ \
    .decCtrl  = LESENSE_DECCTRL_DESC_DEFAULT   /* Default decoder control parameters. */    \
  }

/** Channel descriptor structure. */
typedef struct {
  /** Set to enable scan channel CHx. */
  bool                          enaScanCh;

  /** Set to enable CHx pin. */
  bool                          enaPin;

  /** Enable/disable channel interrupts after configuring all the sensor channel
   *  parameters. */
  bool                          enaInt;

  /** Configure channel pin mode for the excitation phase of the scan sequence.
   *  Note: OPAOUT is only available on channels 2, 3, 4, and 5. */
  LESENSE_ChPinExMode_TypeDef   chPinExMode;

  /** Configure channel pin idle setup in LESENSE idle phase. */
  LESENSE_ChPinIdleMode_TypeDef chPinIdleMode;

  /** Set to use alternate excite pin for excitation. */
  bool                          useAltEx;

  /** Set to enable result from this channel being shifted into the decoder
   *  register. */
  bool                          shiftRes;

  /** Set to invert result bit stored in the SCANRES register. */
  bool                          invRes;

  /** Set to store counter value in the RAM (accessible via RESDATA) and make
   *  the comparison result available in the SCANRES register. */
  LESENSE_StoreSample_TypeDef   storeCntRes;

  /** Select clock used for the excitation timing. */
  LESENSE_ChClk_TypeDef         exClk;

  /** Select clock used for the sample delay timing. */
  LESENSE_ChClk_TypeDef         sampleClk;

  /** Configure the excitation time. Excitation will last exTime+1 excitation clock
   *  cycles. Valid range: 0-63 (6 bits). */
  uint8_t                       exTime;

  /** Configure the sample delay. Sampling will occur after sampleDelay+1 sample
   *  clock cycles. Valid range: 0-127 (7 bits) or 0-255 (8 bits) depending on
   *  device. */
  uint8_t                       sampleDelay;

  /** Configure the measure delay. Sensor measuring is delayed for measDelay
   *  excitation clock cycles. Valid range: 0-127 (7 bits) or 0-1023 (10 bits)
   *  depending on device. */
  uint16_t                       measDelay;

  /** Configure the ACMP threshold or the DAC data.
   *  If perCtrl.dacCh0Data or perCtrl.dacCh1Data is set to #lesenseDACIfData,
   *  acmpThres defines the 12-bit DAC data in the corresponding data register
   *  of DAC interface (DACn_CH0DATA and DACn_CH1DATA).
   *  In this case, the valid range is: 0-4095 (12 bits).
   *  If perCtrl.dacCh0Data or perCtrl.dacCh1Data is set to lesenseACMPThres,
   *  acmpThres defines the 6-bit Vdd scaling factor of ACMP negative input
   *  (VDDLEVEL in ACMP_INPUTSEL register).
   *  In this case, the valid range is: 0-63 (6 bits). */
  uint16_t                     acmpThres;

  /** Select if the ACMP output, the ADC output or the counter output should be used in
   *  comparison. */
  LESENSE_ChSampleMode_TypeDef sampleMode;

  /** Configure the interrupt generation mode for the CHx interrupt flag. */
  LESENSE_ChIntMode_TypeDef    intMode;

  /** Configure the decision threshold for the sensor data comparison.
   *  Valid range: 0-65535 (16 bits). */
  uint16_t                     cntThres;

  /** Select the mode for counter comparison. */
  LESENSE_ChCompMode_TypeDef   compMode;

#if defined(_LESENSE_CH_EVAL_MODE_MASK) || defined(_LESENSE_CH_EVALCFG_MODE_MASK)
  /** Select the sensor evaluation mode. */
  LESENSE_ChEvalMode_TypeDef   evalMode;
#endif
#if defined(_LESENSE_CH_INTERACT_OFFSET_MASK)
  /** Offset for IADC/ACMP interaction.
   * ACMP: offset determines which of the port I/O pins on the external override interface
   * to access.
   * IADC: offset determines which of the IADC scanner channels is sampled. */
  uint8_t  offset;
#endif
} LESENSE_ChDesc_TypeDef;

/** Configuration structure for all the scan channels. */
typedef struct {
  /** Channel descriptor for all the LESENSE channels. */
  LESENSE_ChDesc_TypeDef Ch[LESENSE_NUM_CHANNELS];
} LESENSE_ChAll_TypeDef;

/** Default configuration for the scan channel. */
#if defined(_LESENSE_CH_EVALCFG_MODE_MASK) && defined(_LESENSE_CH_INTERACT_OFFSET_MASK)
#define LESENSE_CH_CONF_DEFAULT                                                                          \
  {                                                                                                      \
    false,                    /* Disable scan channel. */                                                \
    false,                    /* Disable assigned pin on scan channel. */                                \
    false,                    /* Disable interrupts on channel. */                                       \
    lesenseChPinExDis,        /* Channel pin is disabled during excitation period. */                    \
    lesenseChPinIdleDis,      /* Channel pin is disabled during idle period. */                          \
    false,                    /* Do not use alternate excitation pins for excitation. */                 \
    false,                    /* Disabled to shift results from this channel to decoder register.     */ \
    false,                    /* Disabled to invert scan result bit. */                                  \
    lesenseStoreSampleDisable,/* Disabled to store counter value in result buffer. */                    \
    lesenseClkLF,             /* Use LF clock for excitation timing. */                                  \
    lesenseClkLF,             /* Use LF clock for sample timing. */                                      \
    0x00U,                    /* Excitation time is set to 0(+1) excitation clock cycles. */             \
    0x00U,                    /* Sample delay is set to 0(+1) sample clock cycles. */                    \
    0x00U,                    /* Measure delay is set to 0 excitation clock cycles.*/                    \
    0x00U,                    /* ACMP threshold has been set to 0. */                                    \
    lesenseSampleModeACMP,    /* ACMP output will be used in comparison. */                              \
    lesenseSetIntNone,        /* No interrupt is generated by the channel. */                            \
    0x00U,                    /* Counter threshold has bee set to 0x00. */                               \
    lesenseCompModeLess,      /* Compare mode has been set to trigger interrupt on "less". */            \
    lesenseEvalModeThreshold, /* Evaluation mode has been set to trigger interrupt on threshold. */      \
    0x00U                     /* No offset for IADC or ACMP interaction. */                              \
  }
#elif defined(_LESENSE_CH_EVAL_MODE_MASK) /* _SILICON_LABS_32B_SERIES_1 */
#define LESENSE_CH_CONF_DEFAULT                                                                          \
  {                                                                                                      \
    false,                    /* Disable scan channel. */                                                \
    false,                    /* Disable assigned pin on scan channel. */                                \
    false,                    /* Disable interrupts on channel. */                                       \
    lesenseChPinExDis,        /* Channel pin is disabled during excitation period. */                    \
    lesenseChPinIdleDis,      /* Channel pin is disabled during idle period. */                          \
    false,                    /* Do not use alternate excitation pins for excitation. */                 \
    false,                    /* Disabled to shift results from this channel to decoder register.     */ \
    false,                    /* Disabled to invert scan result bit. */                                  \
    lesenseStoreSampleDisable,/* Disabled to store counter value in result buffer. */                    \
    lesenseClkLF,             /* Use LF clock for excitation timing. */                                  \
    lesenseClkLF,             /* Use LF clock for sample timing. */                                      \
    0x00U,                    /* Excitation time is set to 0(+1) excitation clock cycles. */             \
    0x00U,                    /* Sample delay is set to 0(+1) sample clock cycles. */                    \
    0x00U,                    /* Measure delay is set to 0 excitation clock cycles.*/                    \
    0x00U,                    /* ACMP threshold has been set to 0. */                                    \
    lesenseSampleModeACMP,    /* ACMP output will be used in comparison. */                              \
    lesenseSetIntNone,        /* No interrupt is generated by the channel. */                            \
    0x00U,                    /* Counter threshold has bee set to 0x00. */                               \
    lesenseCompModeLess,      /* Compare mode has been set to trigger interrupt on "less". */            \
    lesenseEvalModeThreshold  /* Evaluation mode has been set to trigger interrupt on threshold. */      \
  }
#else /* _SILICON_LABS_32B_SERIES_0 */
#define LESENSE_CH_CONF_DEFAULT                                                                          \
  {                                                                                                      \
    false,                    /* Disable scan channel. */                                                \
    false,                    /* Disable assigned pin on scan channel. */                                \
    false,                    /* Disable interrupts on channel. */                                       \
    lesenseChPinExDis,        /* Channel pin is disabled during excitation period. */                    \
    lesenseChPinIdleDis,      /* Channel pin is disabled during idle period. */                          \
    false,                    /* Do not use alternate excitation pins for excitation. */                 \
    false,                    /* Disabled to shift results from this channel to decoder register.     */ \
    false,                    /* Disabled to invert scan result bit. */                                  \
    lesenseStoreSampleDisable,/* Disabled to store counter value in result buffer. */                    \
    lesenseClkLF,             /* Use LF clock for excitation timing. */                                  \
    lesenseClkLF,             /* Use LF clock for sample timing. */                                      \
    0x00U,                    /* Excitation time is set to 0(+1) excitation clock cycles. */             \
    0x00U,                    /* Sample delay is set to 0(+1) sample clock cycles. */                    \
    0x00U,                    /* Measure delay is set to 0 excitation clock cycles.*/                    \
    0x00U,                    /* ACMP threshold has been set to 0. */                                    \
    lesenseSampleModeACMP,    /* ACMP output will be used in comparison. */                              \
    lesenseSetIntNone,        /* No interrupt is generated by the channel. */                            \
    0x00U,                    /* Counter threshold has bee set to 0x00. */                               \
    lesenseCompModeLess       /* Compare mode has been set to trigger interrupt on "less". */            \
  }
#endif

/** Default configuration for all the sensor channels. */
#define LESENSE_SCAN_CONF_DEFAULT                     \
  {                                                   \
    {                                                 \
      LESENSE_CH_CONF_DEFAULT, /* Scan channel 0. */  \
      LESENSE_CH_CONF_DEFAULT, /* Scan channel 1. */  \
      LESENSE_CH_CONF_DEFAULT, /* Scan channel 2. */  \
      LESENSE_CH_CONF_DEFAULT, /* Scan channel 3. */  \
      LESENSE_CH_CONF_DEFAULT, /* Scan channel 4. */  \
      LESENSE_CH_CONF_DEFAULT, /* Scan channel 5. */  \
      LESENSE_CH_CONF_DEFAULT, /* Scan channel 6. */  \
      LESENSE_CH_CONF_DEFAULT, /* Scan channel 7. */  \
      LESENSE_CH_CONF_DEFAULT, /* Scan channel 8. */  \
      LESENSE_CH_CONF_DEFAULT, /* Scan channel 9. */  \
      LESENSE_CH_CONF_DEFAULT, /* Scan channel 10. */ \
      LESENSE_CH_CONF_DEFAULT, /* Scan channel 11. */ \
      LESENSE_CH_CONF_DEFAULT, /* Scan channel 12. */ \
      LESENSE_CH_CONF_DEFAULT, /* Scan channel 13. */ \
      LESENSE_CH_CONF_DEFAULT, /* Scan channel 14. */ \
      LESENSE_CH_CONF_DEFAULT, /* Scan channel 15. */ \
    }                                                 \
  }

/** Alternate excitation descriptor structure. */
typedef struct {
  /** Configure alternate excitation pins. If set, the corresponding alternate
   *  excitation pin/signal is enabled. */
  bool                         enablePin;

#if defined(_SILICON_LABS_32B_SERIES_0) || defined(_SILICON_LABS_32B_SERIES_1)
  /** Configure idle phase setup of alternate excitation pins.
     The idleConf parameter is not valid when altExMap==lesenseAltExMapACMP. */
  LESENSE_AltExPinIdle_TypeDef idleConf;

  /** Configure how to control external alternate excitation pins. Only
   *  applies if altExMap has been set to lesenseAltExMapALTEX.
   *  If true, excitation happens on the corresponding alternate excitation
   *  pin during excitation periods of all the enabled channels.
   *  If false, excitation happens on the corresponding alternate excitation
   *  pin ONLY during excitation period of the corresponding channel.
   *  The alwaysEx parameter is not valid when altExMap==lesenseAltExMapACMP. */
  bool                         alwaysEx;
#endif
} LESENSE_AltExDesc_TypeDef;

/** Configuration structure for the alternate excitation. */
typedef struct {
#if defined(_SILICON_LABS_32B_SERIES_0) || defined(_SILICON_LABS_32B_SERIES_1)
  /** Select alternate excitation mapping. */
  LESENSE_AltExMap_TypeDef  altExMap;
#endif

  /** Alternate excitation channel descriptors.
   *  When altExMap==lesenseAltExMapALTEX, only the 8 first descriptors are used.
   *  In this mode they describe the configuration of LES_ALTEX0-7 pins.
   *  When altExMap==lesenseAltExMapACMP, all 16 descriptors are used. In this
   *  mode they describe the configuration of the 16 possible ACMP0-1 excitation
   *  channels. Please refer to the user manual for a complete mapping of
   *  routing.
   *  NOTE:
   *  Some parameters in the descriptors are not valid when
   *  altExMap==lesenseAltExMapACMP. Refer to the definition of the
   *  LESENSE_AltExDesc_TypeDef structure for details regarding which parameters
   *  are valid. */
  LESENSE_AltExDesc_TypeDef AltEx[16];
} LESENSE_ConfAltEx_TypeDef;

/** Default configuration for the alternate excitation channel. */
#if defined(_SILICON_LABS_32B_SERIES_0) || defined(_SILICON_LABS_32B_SERIES_1)
#define LESENSE_ALTEX_CH_CONF_DEFAULT                                          \
  {                                                                            \
    false,               /* Alternate excitation disabled.*/                   \
    lesenseAltExPinIdleDis,/* Alternate excitation pin is disabled in idle. */ \
    false                /* Excite only for corresponding channel. */          \
  }
#else
#define LESENSE_ALTEX_CH_CONF_DEFAULT                     \
  {                                                       \
    false             /* Alternate excitation disabled.*/ \
  }
#endif

/** Default configuration for all the alternate excitation channels. */
#if defined(_SILICON_LABS_32B_SERIES_0) || defined(_SILICON_LABS_32B_SERIES_1)
#if defined(_LESENSE_CTRL_ALTEXMAP_ACMP)
#define LESENSE_ALTEX_CONF_DEFAULT                                          \
  {                                                                         \
    lesenseAltExMapACMP,                                                    \
    {                                                                       \
      LESENSE_ALTEX_CH_CONF_DEFAULT, /* Alternate excitation channel 0. */  \
      LESENSE_ALTEX_CH_CONF_DEFAULT, /* Alternate excitation channel 1. */  \
      LESENSE_ALTEX_CH_CONF_DEFAULT, /* Alternate excitation channel 2. */  \
      LESENSE_ALTEX_CH_CONF_DEFAULT, /* Alternate excitation channel 3. */  \
      LESENSE_ALTEX_CH_CONF_DEFAULT, /* Alternate excitation channel 4. */  \
      LESENSE_ALTEX_CH_CONF_DEFAULT, /* Alternate excitation channel 5. */  \
      LESENSE_ALTEX_CH_CONF_DEFAULT, /* Alternate excitation channel 6. */  \
      LESENSE_ALTEX_CH_CONF_DEFAULT, /* Alternate excitation channel 7. */  \
      LESENSE_ALTEX_CH_CONF_DEFAULT, /* Alternate excitation channel 8. */  \
      LESENSE_ALTEX_CH_CONF_DEFAULT, /* Alternate excitation channel 9. */  \
      LESENSE_ALTEX_CH_CONF_DEFAULT, /* Alternate excitation channel 10. */ \
      LESENSE_ALTEX_CH_CONF_DEFAULT, /* Alternate excitation channel 11. */ \
      LESENSE_ALTEX_CH_CONF_DEFAULT, /* Alternate excitation channel 12. */ \
      LESENSE_ALTEX_CH_CONF_DEFAULT, /* Alternate excitation channel 13. */ \
      LESENSE_ALTEX_CH_CONF_DEFAULT, /* Alternate excitation channel 14. */ \
      LESENSE_ALTEX_CH_CONF_DEFAULT  /* Alternate excitation channel 15. */ \
    }                                                                       \
  }
#else
#define LESENSE_ALTEX_CONF_DEFAULT                                          \
  {                                                                         \
    lesenseAltExMapCH,                                                      \
    {                                                                       \
      LESENSE_ALTEX_CH_CONF_DEFAULT, /* Alternate excitation channel 0. */  \
      LESENSE_ALTEX_CH_CONF_DEFAULT, /* Alternate excitation channel 1. */  \
      LESENSE_ALTEX_CH_CONF_DEFAULT, /* Alternate excitation channel 2. */  \
      LESENSE_ALTEX_CH_CONF_DEFAULT, /* Alternate excitation channel 3. */  \
      LESENSE_ALTEX_CH_CONF_DEFAULT, /* Alternate excitation channel 4. */  \
      LESENSE_ALTEX_CH_CONF_DEFAULT, /* Alternate excitation channel 5. */  \
      LESENSE_ALTEX_CH_CONF_DEFAULT, /* Alternate excitation channel 6. */  \
      LESENSE_ALTEX_CH_CONF_DEFAULT, /* Alternate excitation channel 7. */  \
      LESENSE_ALTEX_CH_CONF_DEFAULT, /* Alternate excitation channel 8. */  \
      LESENSE_ALTEX_CH_CONF_DEFAULT, /* Alternate excitation channel 9. */  \
      LESENSE_ALTEX_CH_CONF_DEFAULT, /* Alternate excitation channel 10. */ \
      LESENSE_ALTEX_CH_CONF_DEFAULT, /* Alternate excitation channel 11. */ \
      LESENSE_ALTEX_CH_CONF_DEFAULT, /* Alternate excitation channel 12. */ \
      LESENSE_ALTEX_CH_CONF_DEFAULT, /* Alternate excitation channel 13. */ \
      LESENSE_ALTEX_CH_CONF_DEFAULT, /* Alternate excitation channel 14. */ \
      LESENSE_ALTEX_CH_CONF_DEFAULT  /* Alternate excitation channel 15. */ \
    }                                                                       \
  }
#endif
#else
#define LESENSE_ALTEX_CONF_DEFAULT                                          \
  {                                                                         \
    {                                                                       \
      LESENSE_ALTEX_CH_CONF_DEFAULT, /* Alternate excitation channel 0. */  \
      LESENSE_ALTEX_CH_CONF_DEFAULT, /* Alternate excitation channel 1. */  \
      LESENSE_ALTEX_CH_CONF_DEFAULT, /* Alternate excitation channel 2. */  \
      LESENSE_ALTEX_CH_CONF_DEFAULT, /* Alternate excitation channel 3. */  \
      LESENSE_ALTEX_CH_CONF_DEFAULT, /* Alternate excitation channel 4. */  \
      LESENSE_ALTEX_CH_CONF_DEFAULT, /* Alternate excitation channel 5. */  \
      LESENSE_ALTEX_CH_CONF_DEFAULT, /* Alternate excitation channel 6. */  \
      LESENSE_ALTEX_CH_CONF_DEFAULT, /* Alternate excitation channel 7. */  \
      LESENSE_ALTEX_CH_CONF_DEFAULT, /* Alternate excitation channel 8. */  \
      LESENSE_ALTEX_CH_CONF_DEFAULT, /* Alternate excitation channel 9. */  \
      LESENSE_ALTEX_CH_CONF_DEFAULT, /* Alternate excitation channel 10. */ \
      LESENSE_ALTEX_CH_CONF_DEFAULT, /* Alternate excitation channel 11. */ \
      LESENSE_ALTEX_CH_CONF_DEFAULT, /* Alternate excitation channel 12. */ \
      LESENSE_ALTEX_CH_CONF_DEFAULT, /* Alternate excitation channel 13. */ \
      LESENSE_ALTEX_CH_CONF_DEFAULT, /* Alternate excitation channel 14. */ \
      LESENSE_ALTEX_CH_CONF_DEFAULT /* Alternate excitation channel 15. */  \
    }                                                                       \
  }
#endif

/** Decoder state condition descriptor structure. */
typedef struct {
  /** Configure compare value. State transition is triggered when the sensor state
   *  equals to this value. Valid range: 0-15 (4 bits). */
  uint8_t                    compVal;

  /** Configure compare mask. Set bit X to exclude sensor X from evaluation.
   *  Note: decoder can handle sensor inputs from up to 4 sensors; therefore,
   *  this mask is 4 bit long. */
  uint8_t                    compMask;

#if defined(_SILICON_LABS_32B_SERIES_2)
  /** Configure index of the current state when evaluation is done.
   *  Valid range: 0-15 (4 bits). */
  uint8_t                    curState;
#endif

  /** Configure index of state to be entered if the sensor state equals to
   *  compVal. Valid range: 0-15 (4 bits). */
  uint8_t                    nextState;

  /** Configure which PRS action to perform when the sensor state equals to
   *  compVal. */
  LESENSE_StTransAct_TypeDef prsAct;

  /** If enabled, interrupt flag is set when sensor state equals to compVal. */
  bool                       setInt;
} LESENSE_DecStCond_TypeDef;

/** Default configuration for the decoder state condition. */
#if defined(_SILICON_LABS_32B_SERIES_0) || defined(_SILICON_LABS_32B_SERIES_1)
#define LESENSE_ST_CONF_DEFAULT                                          \
  {                                                                      \
    0x0FU,             /* Compare value set to 0x0F. */                  \
    0x00U,             /* All decoder inputs masked. */                  \
    0U,                /* Next state is state 0. */                      \
    lesenseTransActNone, /* No PRS action performed on compare match. */ \
    false              /* No interrupt triggered on compare match. */    \
  }
#else
#define LESENSE_ST_CONF_DEFAULT                                          \
  {                                                                      \
    0x0FU,               /* Compare value set to 0x0F. */                \
    0x00U,               /* All decoder inputs masked. */                \
    0U,                  /* Current state must be state 0. */            \
    0U,                  /* Next state is state 0. */                    \
    lesenseTransActNone, /* No PRS action performed on compare match. */ \
    false                /* No interrupt triggered on compare match. */  \
  }
#endif

/** Decoder state x configuration structure. */
#if defined(_SILICON_LABS_32B_SERIES_0) || defined(_SILICON_LABS_32B_SERIES_1)
typedef struct {
  /** If enabled, the state descriptor pair in next location will also be
   *  evaluated. */
  bool                      chainDesc;

  /** State condition descriptor A (high level descriptor of
   *  LESENSE_STx_DECCONFA). */
  LESENSE_DecStCond_TypeDef confA;

  /** State condition descriptor B (high level descriptor of
   *  LESENSE_STx_DECCONFB). */
  LESENSE_DecStCond_TypeDef confB;
} LESENSE_DecStDesc_TypeDef;
#else
typedef LESENSE_DecStCond_TypeDef LESENSE_DecStDesc_TypeDef;
#endif

/** Configuration structure for decoder. */
typedef struct {
#if defined(_SILICON_LABS_32B_SERIES_0) || defined(_SILICON_LABS_32B_SERIES_1)
  /** Descriptor of the 16 or 32 decoder states depending on the device. */
  LESENSE_DecStDesc_TypeDef St[LESENSE_NUM_DECODER_STATES];
#else
  /** Descriptor of the 64 Arcs on series 2 devices. */
  LESENSE_DecStDesc_TypeDef St[LESENSE_NUM_ARCS];
#endif
} LESENSE_DecStAll_TypeDef;

/** Default configuration for all decoder states. */
#if defined(_SILICON_LABS_32B_SERIES_0)
#define LESENSE_DECODER_CONF_DEFAULT                                                       \
  { /* chain |   Descriptor A         |   Descriptor B   */                                \
    {                                                                                      \
      { false, LESENSE_ST_CONF_DEFAULT, LESENSE_ST_CONF_DEFAULT }, /* Decoder state 0. */  \
      { false, LESENSE_ST_CONF_DEFAULT, LESENSE_ST_CONF_DEFAULT }, /* Decoder state 1. */  \
      { false, LESENSE_ST_CONF_DEFAULT, LESENSE_ST_CONF_DEFAULT }, /* Decoder state 2. */  \
      { false, LESENSE_ST_CONF_DEFAULT, LESENSE_ST_CONF_DEFAULT }, /* Decoder state 3. */  \
      { false, LESENSE_ST_CONF_DEFAULT, LESENSE_ST_CONF_DEFAULT }, /* Decoder state 4. */  \
      { false, LESENSE_ST_CONF_DEFAULT, LESENSE_ST_CONF_DEFAULT }, /* Decoder state 5. */  \
      { false, LESENSE_ST_CONF_DEFAULT, LESENSE_ST_CONF_DEFAULT }, /* Decoder state 6. */  \
      { false, LESENSE_ST_CONF_DEFAULT, LESENSE_ST_CONF_DEFAULT }, /* Decoder state 7. */  \
      { false, LESENSE_ST_CONF_DEFAULT, LESENSE_ST_CONF_DEFAULT }, /* Decoder state 8. */  \
      { false, LESENSE_ST_CONF_DEFAULT, LESENSE_ST_CONF_DEFAULT }, /* Decoder state 9. */  \
      { false, LESENSE_ST_CONF_DEFAULT, LESENSE_ST_CONF_DEFAULT }, /* Decoder state 10. */ \
      { false, LESENSE_ST_CONF_DEFAULT, LESENSE_ST_CONF_DEFAULT }, /* Decoder state 11. */ \
      { false, LESENSE_ST_CONF_DEFAULT, LESENSE_ST_CONF_DEFAULT }, /* Decoder state 12. */ \
      { false, LESENSE_ST_CONF_DEFAULT, LESENSE_ST_CONF_DEFAULT }, /* Decoder state 13. */ \
      { false, LESENSE_ST_CONF_DEFAULT, LESENSE_ST_CONF_DEFAULT }, /* Decoder state 14. */ \
      { false, LESENSE_ST_CONF_DEFAULT, LESENSE_ST_CONF_DEFAULT }  /* Decoder state 15. */ \
    }                                                                                      \
  }
#elif defined(_SILICON_LABS_32B_SERIES_1)
#define LESENSE_DECODER_CONF_DEFAULT                                                       \
  { /* chain |   Descriptor A         |   Descriptor B   */                                \
    {                                                                                      \
      { false, LESENSE_ST_CONF_DEFAULT, LESENSE_ST_CONF_DEFAULT }, /* Decoder state 0. */  \
      { false, LESENSE_ST_CONF_DEFAULT, LESENSE_ST_CONF_DEFAULT }, /* Decoder state 1. */  \
      { false, LESENSE_ST_CONF_DEFAULT, LESENSE_ST_CONF_DEFAULT }, /* Decoder state 2. */  \
      { false, LESENSE_ST_CONF_DEFAULT, LESENSE_ST_CONF_DEFAULT }, /* Decoder state 3. */  \
      { false, LESENSE_ST_CONF_DEFAULT, LESENSE_ST_CONF_DEFAULT }, /* Decoder state 4. */  \
      { false, LESENSE_ST_CONF_DEFAULT, LESENSE_ST_CONF_DEFAULT }, /* Decoder state 5. */  \
      { false, LESENSE_ST_CONF_DEFAULT, LESENSE_ST_CONF_DEFAULT }, /* Decoder state 6. */  \
      { false, LESENSE_ST_CONF_DEFAULT, LESENSE_ST_CONF_DEFAULT }, /* Decoder state 7. */  \
      { false, LESENSE_ST_CONF_DEFAULT, LESENSE_ST_CONF_DEFAULT }, /* Decoder state 8. */  \
      { false, LESENSE_ST_CONF_DEFAULT, LESENSE_ST_CONF_DEFAULT }, /* Decoder state 9. */  \
      { false, LESENSE_ST_CONF_DEFAULT, LESENSE_ST_CONF_DEFAULT }, /* Decoder state 10. */ \
      { false, LESENSE_ST_CONF_DEFAULT, LESENSE_ST_CONF_DEFAULT }, /* Decoder state 11. */ \
      { false, LESENSE_ST_CONF_DEFAULT, LESENSE_ST_CONF_DEFAULT }, /* Decoder state 12. */ \
      { false, LESENSE_ST_CONF_DEFAULT, LESENSE_ST_CONF_DEFAULT }, /* Decoder state 13. */ \
      { false, LESENSE_ST_CONF_DEFAULT, LESENSE_ST_CONF_DEFAULT }, /* Decoder state 14. */ \
      { false, LESENSE_ST_CONF_DEFAULT, LESENSE_ST_CONF_DEFAULT }, /* Decoder state 15. */ \
      { false, LESENSE_ST_CONF_DEFAULT, LESENSE_ST_CONF_DEFAULT }, /* Decoder state 16. */ \
      { false, LESENSE_ST_CONF_DEFAULT, LESENSE_ST_CONF_DEFAULT }, /* Decoder state 17. */ \
      { false, LESENSE_ST_CONF_DEFAULT, LESENSE_ST_CONF_DEFAULT }, /* Decoder state 18. */ \
      { false, LESENSE_ST_CONF_DEFAULT, LESENSE_ST_CONF_DEFAULT }, /* Decoder state 19. */ \
      { false, LESENSE_ST_CONF_DEFAULT, LESENSE_ST_CONF_DEFAULT }, /* Decoder state 20. */ \
      { false, LESENSE_ST_CONF_DEFAULT, LESENSE_ST_CONF_DEFAULT }, /* Decoder state 21. */ \
      { false, LESENSE_ST_CONF_DEFAULT, LESENSE_ST_CONF_DEFAULT }, /* Decoder state 22. */ \
      { false, LESENSE_ST_CONF_DEFAULT, LESENSE_ST_CONF_DEFAULT }, /* Decoder state 23. */ \
      { false, LESENSE_ST_CONF_DEFAULT, LESENSE_ST_CONF_DEFAULT }, /* Decoder state 24. */ \
      { false, LESENSE_ST_CONF_DEFAULT, LESENSE_ST_CONF_DEFAULT }, /* Decoder state 25. */ \
      { false, LESENSE_ST_CONF_DEFAULT, LESENSE_ST_CONF_DEFAULT }, /* Decoder state 26. */ \
      { false, LESENSE_ST_CONF_DEFAULT, LESENSE_ST_CONF_DEFAULT }, /* Decoder state 27. */ \
      { false, LESENSE_ST_CONF_DEFAULT, LESENSE_ST_CONF_DEFAULT }, /* Decoder state 28. */ \
      { false, LESENSE_ST_CONF_DEFAULT, LESENSE_ST_CONF_DEFAULT }, /* Decoder state 29. */ \
      { false, LESENSE_ST_CONF_DEFAULT, LESENSE_ST_CONF_DEFAULT }, /* Decoder state 30. */ \
      { false, LESENSE_ST_CONF_DEFAULT, LESENSE_ST_CONF_DEFAULT }  /* Decoder state 31. */ \
    }                                                                                      \
  }
#else
#define LESENSE_DECODER_CONF_DEFAULT                   \
  {                                                    \
    {                                                  \
      LESENSE_ST_CONF_DEFAULT, /* Decoder state 0. */  \
      LESENSE_ST_CONF_DEFAULT, /* Decoder state 1. */  \
      LESENSE_ST_CONF_DEFAULT, /* Decoder state 2. */  \
      LESENSE_ST_CONF_DEFAULT, /* Decoder state 3. */  \
      LESENSE_ST_CONF_DEFAULT, /* Decoder state 4. */  \
      LESENSE_ST_CONF_DEFAULT, /* Decoder state 5. */  \
      LESENSE_ST_CONF_DEFAULT, /* Decoder state 6. */  \
      LESENSE_ST_CONF_DEFAULT, /* Decoder state 7. */  \
      LESENSE_ST_CONF_DEFAULT, /* Decoder state 8. */  \
      LESENSE_ST_CONF_DEFAULT, /* Decoder state 9. */  \
      LESENSE_ST_CONF_DEFAULT, /* Decoder state 10. */ \
      LESENSE_ST_CONF_DEFAULT, /* Decoder state 11. */ \
      LESENSE_ST_CONF_DEFAULT, /* Decoder state 12. */ \
      LESENSE_ST_CONF_DEFAULT, /* Decoder state 13. */ \
      LESENSE_ST_CONF_DEFAULT, /* Decoder state 14. */ \
      LESENSE_ST_CONF_DEFAULT, /* Decoder state 15. */ \
      LESENSE_ST_CONF_DEFAULT, /* Decoder state 16. */ \
      LESENSE_ST_CONF_DEFAULT, /* Decoder state 17. */ \
      LESENSE_ST_CONF_DEFAULT, /* Decoder state 18. */ \
      LESENSE_ST_CONF_DEFAULT, /* Decoder state 19. */ \
      LESENSE_ST_CONF_DEFAULT, /* Decoder state 20. */ \
      LESENSE_ST_CONF_DEFAULT, /* Decoder state 21. */ \
      LESENSE_ST_CONF_DEFAULT, /* Decoder state 22. */ \
      LESENSE_ST_CONF_DEFAULT, /* Decoder state 23. */ \
      LESENSE_ST_CONF_DEFAULT, /* Decoder state 24. */ \
      LESENSE_ST_CONF_DEFAULT, /* Decoder state 25. */ \
      LESENSE_ST_CONF_DEFAULT, /* Decoder state 26. */ \
      LESENSE_ST_CONF_DEFAULT, /* Decoder state 27. */ \
      LESENSE_ST_CONF_DEFAULT, /* Decoder state 28. */ \
      LESENSE_ST_CONF_DEFAULT, /* Decoder state 29. */ \
      LESENSE_ST_CONF_DEFAULT, /* Decoder state 30. */ \
      LESENSE_ST_CONF_DEFAULT  /* Decoder state 31. */ \
    }                                                  \
  }
#endif

/*******************************************************************************
 *****************************   PROTOTYPES   **********************************
 ******************************************************************************/
void LESENSE_Init(const LESENSE_Init_TypeDef * init, bool reqReset);
void LESENSE_Reset(void);

uint32_t LESENSE_ScanFreqSet(uint32_t refFreq, uint32_t scanFreq);
void LESENSE_ScanModeSet(LESENSE_ScanMode_TypeDef scanMode, bool start);
void LESENSE_StartDelaySet(uint8_t startDelay);
void LESENSE_ClkDivSet(LESENSE_ChClk_TypeDef clk,
                       LESENSE_ClkPresc_TypeDef clkDiv);

void LESENSE_ChannelAllConfig(const LESENSE_ChAll_TypeDef * confChAll);
void LESENSE_ChannelConfig(const LESENSE_ChDesc_TypeDef * confCh,
                           uint32_t chIdx);
void LESENSE_ChannelEnable(uint8_t chIdx,
                           bool enaScanCh,
                           bool enaPin);
void LESENSE_ChannelEnableMask(uint16_t chMask, uint16_t pinMask);
void LESENSE_ChannelTimingSet(uint8_t chIdx,
                              uint8_t exTime,
                              uint8_t sampleDelay,
                              uint16_t measDelay);
void LESENSE_ChannelThresSet(uint8_t chIdx,
                             uint16_t acmpThres,
                             uint16_t cntThres);
#if defined(_LESENSE_CH_EVAL_MODE_MASK) || defined(_LESENSE_CH_EVALCFG_MODE_MASK)
void LESENSE_ChannelSlidingWindow(uint8_t chIdx,
                                  uint32_t windowSize,
                                  uint32_t initValue);
void LESENSE_ChannelStepDetection(uint8_t chIdx,
                                  uint32_t stepSize,
                                  uint32_t initValue);
void LESENSE_WindowSizeSet(uint32_t windowSize);
void LESENSE_StepSizeSet(uint32_t stepSize);
#endif

void LESENSE_AltExConfig(const LESENSE_ConfAltEx_TypeDef * confAltEx);

void LESENSE_DecoderStateAllConfig(const LESENSE_DecStAll_TypeDef * confDecStAll);
void LESENSE_DecoderStateConfig(const LESENSE_DecStDesc_TypeDef * confDecSt,
                                uint32_t decSt);
#if defined(_SILICON_LABS_32B_SERIES_0) || defined(_SILICON_LABS_32B_SERIES_1)
void LESENSE_DecoderStateSet(uint32_t decSt);
#endif
uint32_t LESENSE_DecoderStateGet(void);
#if defined(_LESENSE_PRSCTRL_MASK)
void LESENSE_DecoderPrsOut(bool enable, uint32_t decMask, uint32_t decCmp);
#endif

void LESENSE_ScanStart(void);
void LESENSE_ScanStop(void);
void LESENSE_DecoderStart(void);
void LESENSE_ResultBufferClear(void);

/***************************************************************************//**
 * @brief
 *   Stop LESENSE decoder.
 *
 * @details
 *   Disables LESENSE decoder by setting the command to
 *   LESENSE_DECCTRL register.
 ******************************************************************************/
__STATIC_INLINE void LESENSE_DecoderStop(void)
{
  /* Stop decoder */
#if defined(_SILICON_LABS_32B_SERIES_0) || defined(_SILICON_LABS_32B_SERIES_1)
  LESENSE->DECCTRL |= LESENSE_DECCTRL_DISABLE;
#else
  LESENSE->DECCTRL |= LESENSE_DECCTRL_DECDIS;
#endif
}

/***************************************************************************//**
 * @brief
 *   Get the current status of LESENSE.
 *
 * @return
 *   Returns the value of the LESENSE_STATUS register that
 *   contains the OR combination of the following status bits for EFR series 0/1:
 *   @li LESENSE_STATUS_BUFDATAV - Result data valid. Set when data is available
 *   in result buffer. Cleared when buffer is empty.
 *   @li LESENSE_STATUS_BUFFULL - Result buffer full. Set when result
 *   buffer is full.
 *   @li LESENSE_STATUS_BUFHALFFULL - Result buffer half full. Set when
 *   result buffer is half full.
 *   @li LESENSE_STATUS_RUNNING - LESENSE is active.
 *   @li LESENSE_STATUS_SCANACTIVE - LESENSE is currently interfacing sensors.
 *
 *   The OR combination of the following status bits for EFR series 2:
 *   @li LESENSE_STATUS_RESFIFOV - Result Fifo valid. Set when data is available
 *   in result Fifo. Cleared when Fifo is empty.
 *   @li LESENSE_STATUS_RESFIFOFULL - Result Fifo full. Set when result
 *   Fifo is full.
 *   @li LESENSE_STATUS_RUNNING - LESENSE is active.
 *   @li LESENSE_STATUS_SCANACTIVE - LESENSE is currently interfacing sensors.
 *   @li LESENSE_STATUS_FLUSHING - Fifo flushing
 *   @li LESENSE_STATUS_READBUSY - Fifo Read busy
 ******************************************************************************/
__STATIC_INLINE uint32_t LESENSE_StatusGet(void)
{
  return LESENSE->STATUS;
}

/***************************************************************************//**
 * @brief
 *   Wait until status of LESENSE is equal to what was requested.
 *
 * @details
 *   Polls LESENSE_STATUS register and waits until
 *   requested combination of flags are set.
 *
 * @param[in] flag
 *   The OR combination of the following status bits for EFR series 0/1:
 *   @li LESENSE_STATUS_BUFDATAV - Result data valid. Set when data is available
 *   in result buffer. Cleared when buffer is empty.
 *   @li LESENSE_STATUS_BUFHALFFULL - Result buffer half full. Set when
 *   result buffer is half full.
 *   @li LESENSE_STATUS_BUFFULL - Result buffer full. Set when result
 *   buffer is full.
 *   @li LESENSE_STATUS_RUNNING - LESENSE is active.
 *   @li LESENSE_STATUS_SCANACTIVE - LESENSE is currently interfacing sensors.
 *   @li LESENSE_STATUS_DACACTIVE - The DAC interface is currently active.

 *   The OR combination of the following status bits for EFR series 2:
 *   @li LESENSE_STATUS_RESFIFOV - Result FIFO valid. Set when data is available
 *   in result FIFO. Cleared when FIFO is empty.
 *   @li LESENSE_STATUS_RESFIFOFULL - Result FIFO full. Set when result
 *   FIFO is full.
 *   @li LESENSE_STATUS_RUNNING - LESENSE is active.
 *   @li LESENSE_STATUS_SCANACTIVE - LESENSE is currently interfacing sensors.
 *   @li LESENSE_STATUS_FLUSHING - FIFO flushing
 *   @li LESENSE_STATUS_READBUSY - FIFO Read busy
 ******************************************************************************/
__STATIC_INLINE void LESENSE_StatusWait(uint32_t flag)
{
  while (!(LESENSE->STATUS & flag))
    ;
}

/***************************************************************************//**
 * @brief
 *   Get the currently active channel index.
 *
 * @return
 *   Returns the value of the LESENSE_CHINDEX register that
 *   contains the index of currently active channel (0-15).
 ******************************************************************************/
__STATIC_INLINE uint32_t LESENSE_ChannelActiveGet(void)
{
  return LESENSE->CURCH;
}

/***************************************************************************//**
 * @brief
 *   Get the latest scan comparison result (1 bit / channel).
 *
 * @return
 *   Returns the value of the LESENSE_SCANRES register that
 *   contains the comparison result of last scan on all channels.
 *   Bit x is set if a comparison triggered on channel x, which means that
 *   LESENSE counter met the comparison criteria set in LESENSE_CHx_EVAL by
 *   COMPMODE and CNTTHRES.
 ******************************************************************************/
__STATIC_INLINE uint32_t LESENSE_ScanResultGet(void)
{
  return LESENSE->SCANRES & _LESENSE_SCANRES_SCANRES_MASK;
}

/***************************************************************************//**
 * @brief
 *   Get the oldest unread data from the result buffer.
 *
 * @note
 *   Make sure that the STORERES bit is set in LESENSE_CHx_EVAL, or
 *   the STRSCANRES bit is set in LESENSE_CTRL; otherwise, returns the
 *   undefined value.
 *
 * @return
 *   Returns the value of LESENSE_RESDATA register that
 *   contains the oldest unread counter result from result buffer.
 ******************************************************************************/
__STATIC_INLINE uint32_t LESENSE_ScanResultDataGet(void)
{
#if defined(_SILICON_LABS_32B_SERIES_0) || defined(_SILICON_LABS_32B_SERIES_1)
  return LESENSE->BUFDATA;
#else
  return LESENSE->RESFIFO;
#endif
}

#if defined(_SILICON_LABS_32B_SERIES_0) || defined(_SILICON_LABS_32B_SERIES_1)
/***************************************************************************//**
 * @brief
 *   Get data from the result data buffer.
 *
 * @note
 *   Make sure that the STORERES bit is set in LESENSE_CHx_EVAL, or
 *   the STRSCANRES bit is set in LESENSE_CTRL; otherwise, returns the
 *   undefined value.
 *
 * @param[in] idx
 *   Result data buffer index. Valid range: 0-15.
 *
 * @return
 *   Returns the selected word from the result data buffer.
 ******************************************************************************/
__STATIC_INLINE uint32_t LESENSE_ScanResultDataBufferGet(uint32_t idx)
{
  /* Note: masking is needed to avoid over-indexing! */
  return LESENSE->BUF[idx & 0x0FU].DATA;
}
#endif

/***************************************************************************//**
 * @brief
 *   Get the current state of the LESENSE sensor.
 *
 * @return
 *   Returns the value of LESENSE_SENSORSTATE register that
 *   represents the current state of the LESENSE sensor.
 ******************************************************************************/
__STATIC_INLINE uint32_t LESENSE_SensorStateGet(void)
{
  return LESENSE->SENSORSTATE;
}

#if defined(LESENSE_POWERDOWN_RAM)
/***************************************************************************//**
 * @brief
 *   Shut off the power to the LESENSE RAM, which disables LESENSE.
 *
 * @details
 *   Shuts off the LESENSE RAM in order to decrease leakage
 *   current of MCU if LESENSE is not used in your application.
 *
 * @note
 *   Warning! Once LESENSE RAM is powered down, it cannot be powered up
 *   again.
 ******************************************************************************/
__STATIC_INLINE void LESENSE_RAMPowerDown(void)
{
  /* Power down the LESENSE RAM */
  LESENSE->POWERDOWN = LESENSE_POWERDOWN_RAM;
}
#endif

/***************************************************************************//**
 * @brief
 *   Clear one or more pending LESENSE interrupts.
 *
 * @param[in] flags
 *   Pending LESENSE interrupt sources to clear. Use a set of interrupt flags
 *   OR-ed together to clear multiple interrupt sources of LESENSE module
 *   (LESENSE_IF_nnn).
 ******************************************************************************/
__STATIC_INLINE void LESENSE_IntClear(uint32_t flags)
{
#if defined(_SILICON_LABS_32B_SERIES_0) || defined(_SILICON_LABS_32B_SERIES_1)
  LESENSE->IFC = flags;
#else
  LESENSE->IF_CLR = flags;
#endif
}

/***************************************************************************//**
 * @brief
 *   Enable one or more LESENSE interrupts.
 *
 * @param[in] flags
 *   LESENSE interrupt sources to enable. Use a set of interrupt flags OR-ed
 *   together to enable multiple interrupt sources of LESENSE module
 *   (LESENSE_IF_nnn).
 ******************************************************************************/
__STATIC_INLINE void LESENSE_IntEnable(uint32_t flags)
{
#if defined(_SILICON_LABS_32B_SERIES_0) || defined(_SILICON_LABS_32B_SERIES_1)
  LESENSE->IEN |= flags;
#else
  LESENSE->IEN_SET = flags;
#endif
}

/***************************************************************************//**
 * @brief
 *   Disable one or more LESENSE interrupts.
 *
 * @param[in] flags
 *   LESENSE interrupt sources to disable. Use a set of interrupt flags OR-ed
 *   together to disable multiple interrupt sources of LESENSE module
 *   (LESENSE_IF_nnn).
 ******************************************************************************/
__STATIC_INLINE void LESENSE_IntDisable(uint32_t flags)
{
#if defined(_SILICON_LABS_32B_SERIES_0) || defined(_SILICON_LABS_32B_SERIES_1)
  LESENSE->IEN &= ~flags;
#else
  LESENSE->IEN_CLR = flags;
#endif
}

/***************************************************************************//**
 * @brief
 *   Set one or more pending LESENSE interrupts from SW.
 *
 * @param[in] flags
 *   LESENSE interrupt sources to set to pending. Use a set of interrupt
 *   flags OR-ed together to set multiple interrupt sources of LESENSE
 *   module (LESENSE_IFS_nnn).
 ******************************************************************************/
__STATIC_INLINE void LESENSE_IntSet(uint32_t flags)
{
#if defined(_SILICON_LABS_32B_SERIES_0) || defined(_SILICON_LABS_32B_SERIES_1)
  LESENSE->IFS = flags;
#else
  LESENSE->IF_SET = flags;
#endif
}

/***************************************************************************//**
 * @brief
 *   Get pending LESENSE interrupt flags.
 *
 * @note
 *   Event bits are not cleared by the use of this function.
 *
 * @return
 *   Pending LESENSE interrupt sources. The OR combination of valid interrupt
 *   flags of the LESENSE module (LESENSE_IF_nnn).
 ******************************************************************************/
__STATIC_INLINE uint32_t LESENSE_IntGet(void)
{
  return LESENSE->IF;
}

/***************************************************************************//**
 * @brief
 *   Get enabled and pending LESENSE interrupt flags.
 *
 * @details
 *   Useful for handling more interrupt sources in the same interrupt handler.
 *
 * @note
 *   Event bits are not cleared by the use of this function.
 *
 * @return
 *   Pending and enabled LESENSE interrupt sources.
 *   Return value is the bitwise AND combination of
 *   - the OR combination of enabled interrupt sources in LESENSE_IEN_nnn
 *   register (LESENSE_IEN_nnn) and
 *   - the OR combination of valid interrupt flags of LESENSE module
 *   (LESENSE_IF_nnn).
 ******************************************************************************/
__STATIC_INLINE uint32_t LESENSE_IntGetEnabled(void)
{
  uint32_t tmp;

  /* Store LESENSE->IEN in temporary variable in order to define explicit order
   * of volatile accesses. */
  tmp = LESENSE->IEN;

  /* Bitwise AND of pending and enabled interrupts */
  return LESENSE->IF & tmp;
}

/** @} (end addtogroup lesense) */

#ifdef __cplusplus
}
#endif

#endif /* defined(LESENSE_COUNT) && (LESENSE_COUNT > 0) */

#endif /* EM_LESENSE_H */
